The-Public-Radio/Embedded_Hardware/EAGLE_CAD/TestFixtures /PRTF01.brd

## EAGLE design EAGLE_CAD/TestFixtures /PRTF01.brd (2015-02-14)

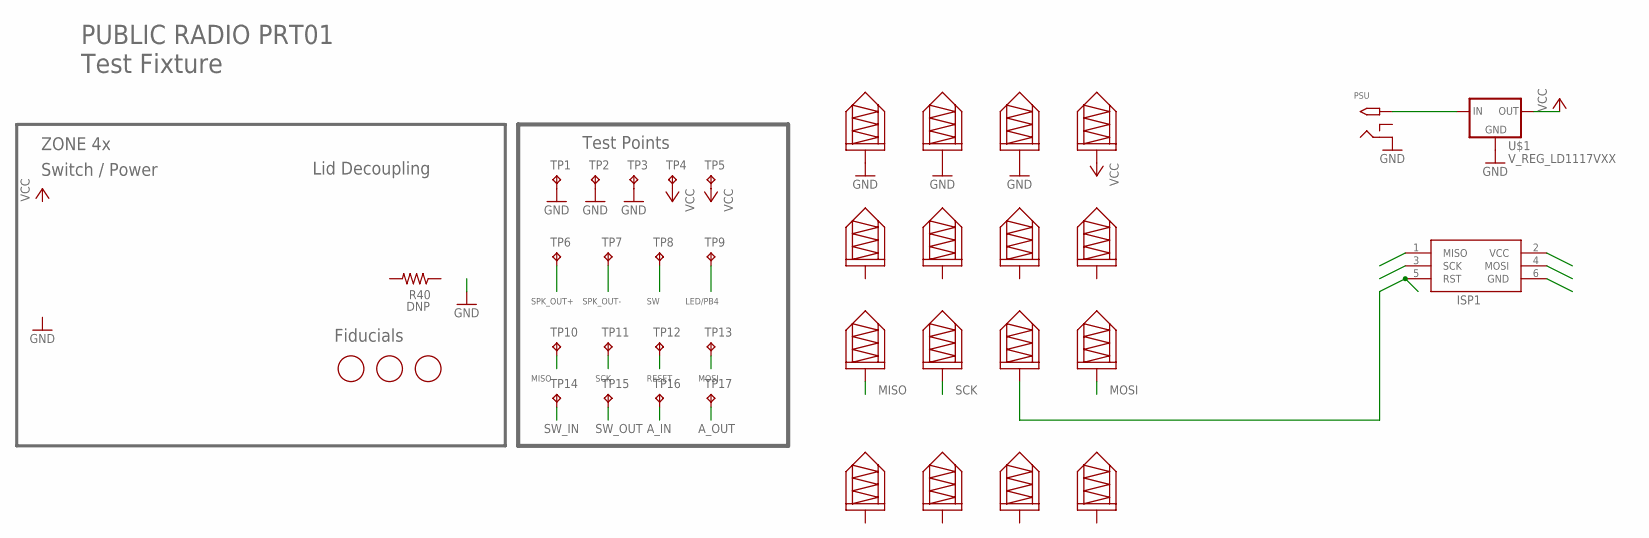
[picture p14: schematic PRTF01.sch]

Parts:
ISP1: AVRISP-6; AVRISP
MARK1, MARK2, MARK3: FIDUCIAL; FIDUCIAL_1MM
P1, P2, P3, P4, P6, P8, P9, P10, P11, P12, P13, P14, P15, P16, P17: 0908MILL_MAX_SPRINGPIN
PSU: 2.1MMJACKTHM; PJ-102A
R40: DNP; 0603_CPL; MFG_PN ERJ-3GEY0R00V
TP1, TP2, TP3, TP4, TP5, TP6, TP7, TP8, TP9, TP10, TP11, TP12, TP13, TP14, TP15, TP16, TP17: TPTP20R; TP20R
U$1: V_REG_LD1117VXX; 78XXL
U$P7: 0908MILL_MAX_SPRINGPIN

Connections:
!RST: TP10.TP
A_IN: TP16.TP
A_OUT: TP17.TP
GND: P1.P$1, P2.P$1, P3.P$1, PSU.RING, TP1.TP, TP2.TP, TP3.TP, U$1.IN (GND)
LED/PB4: TP9.TP
MISO: ISP1.1 (MISO), P10.P$1
MOSI: ISP1.4 (MOSI), P13.P$1
unnamed: PSU.TIP, U$1.OUT (IN)
RESET: ISP1.5 (RST), P12.P$1, TP12.TP
SCK: ISP1.3 (SCK), P11.P$1
SCLK: TP11.TP
SDIO: TP13.TP
SPK_OUT+: TP6.TP
SPK_OUT-: TP7.TP
SW: TP8.TP
SW_IN: TP14.TP
SW_OUT: TP15.TP
VCC: P4.P$1, TP4.TP, TP5.TP, U$1.GND (OUT)

Notes on the sheet:
Switch / Power
Lid Decoupling
PUBLIC RADIO PRT01 Test Fixture
Fiducials
Test Points
MISO
SCK
RESET
MOSI
ZONE 4x
