The-Public-Radio/Embedded_Hardware/EAGLE_CAD/TestFixtures /PRTF01.brd

## EAGLE design EAGLE_CAD/TestFixtures /PRTF01.brd (continued)

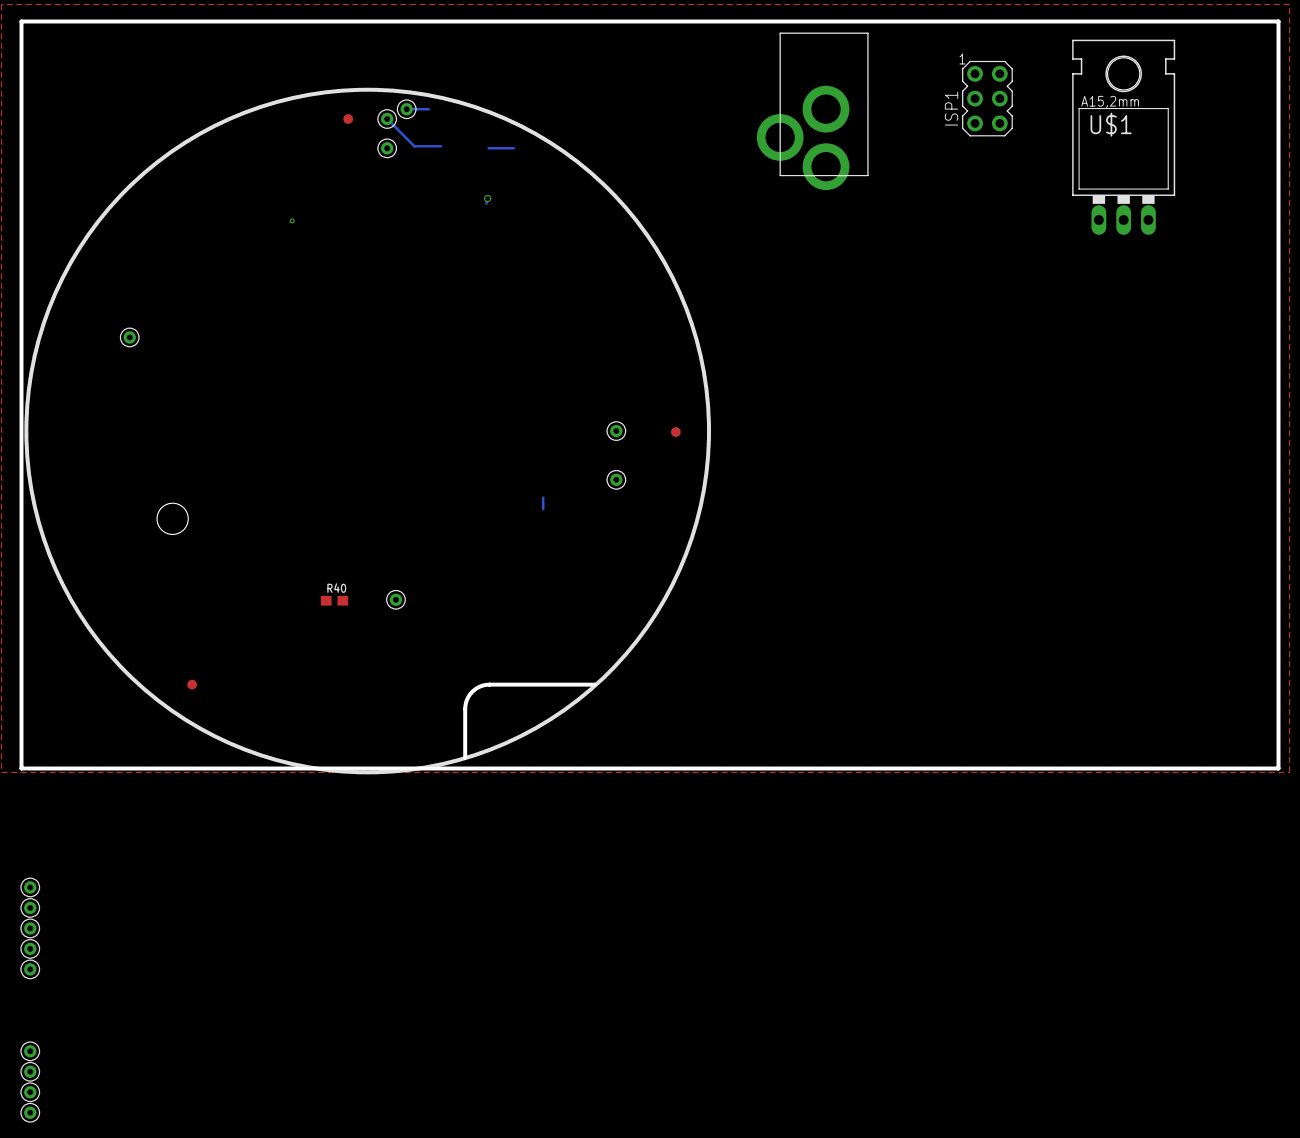
[picture p15: board PRTF01.brd from above]

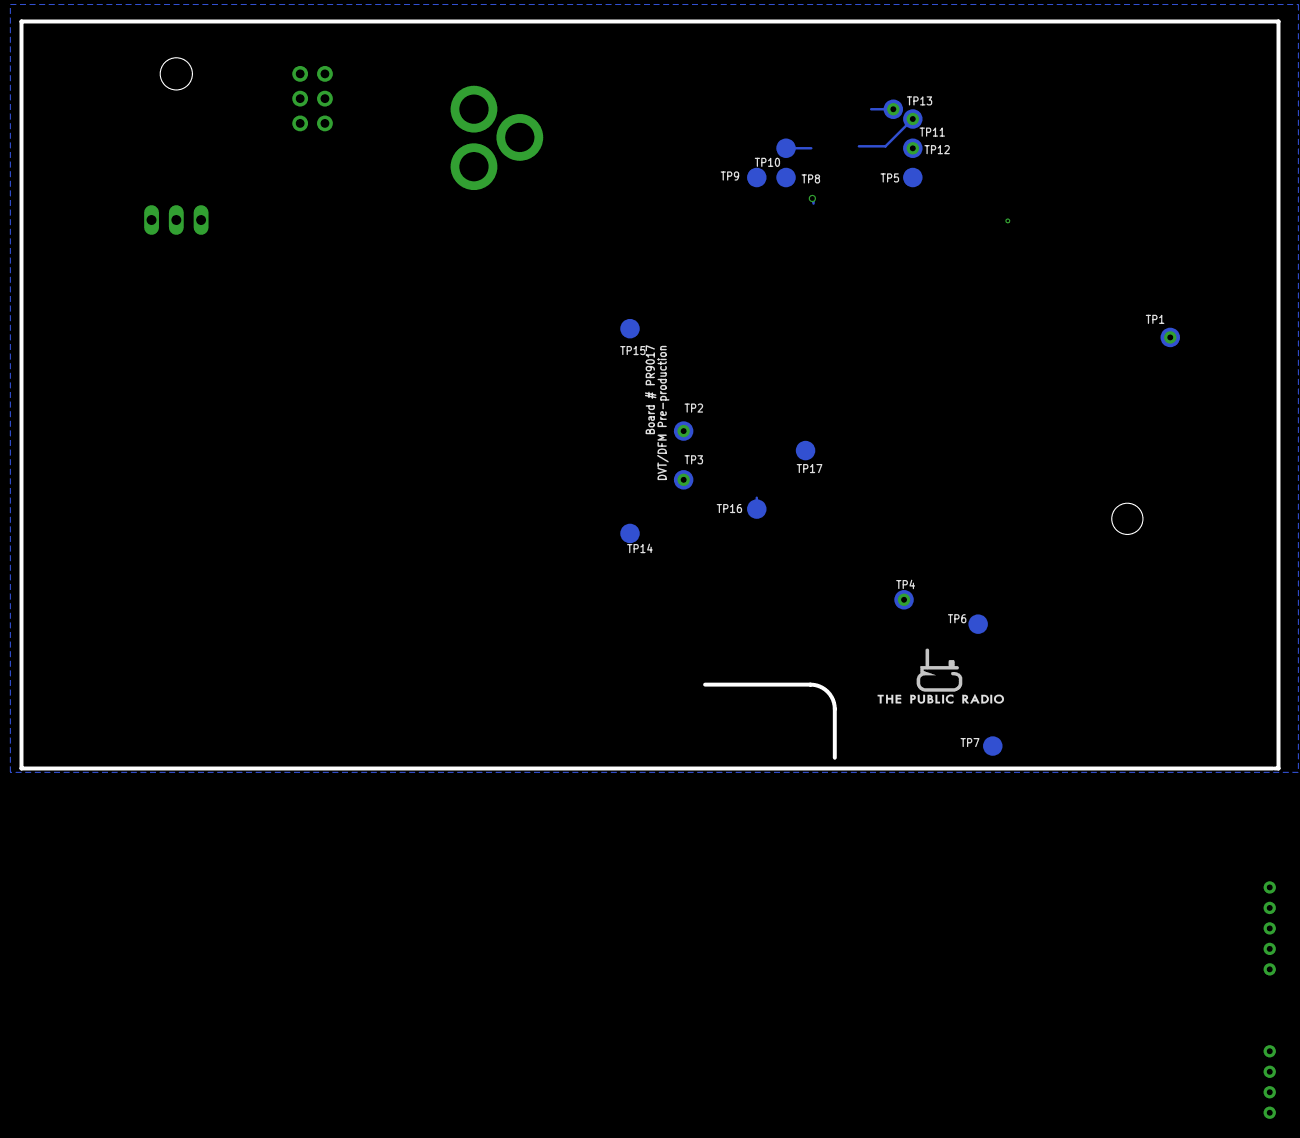
[picture p16: board PRTF01.brd from below]

Board: 2 copper layers, 128.9 x 76.6 mm, 40 parts (17 on the bottom side), 7 nets.
