The-Public-Radio/Embedded_Hardware/EAGLE_CAD/PR9018ProductionFiles/Eagle/PR9018.brd

## EAGLE design EAGLE_CAD/PR9018ProductionFiles/Eagle/PR9018.brd (2015-02-14)

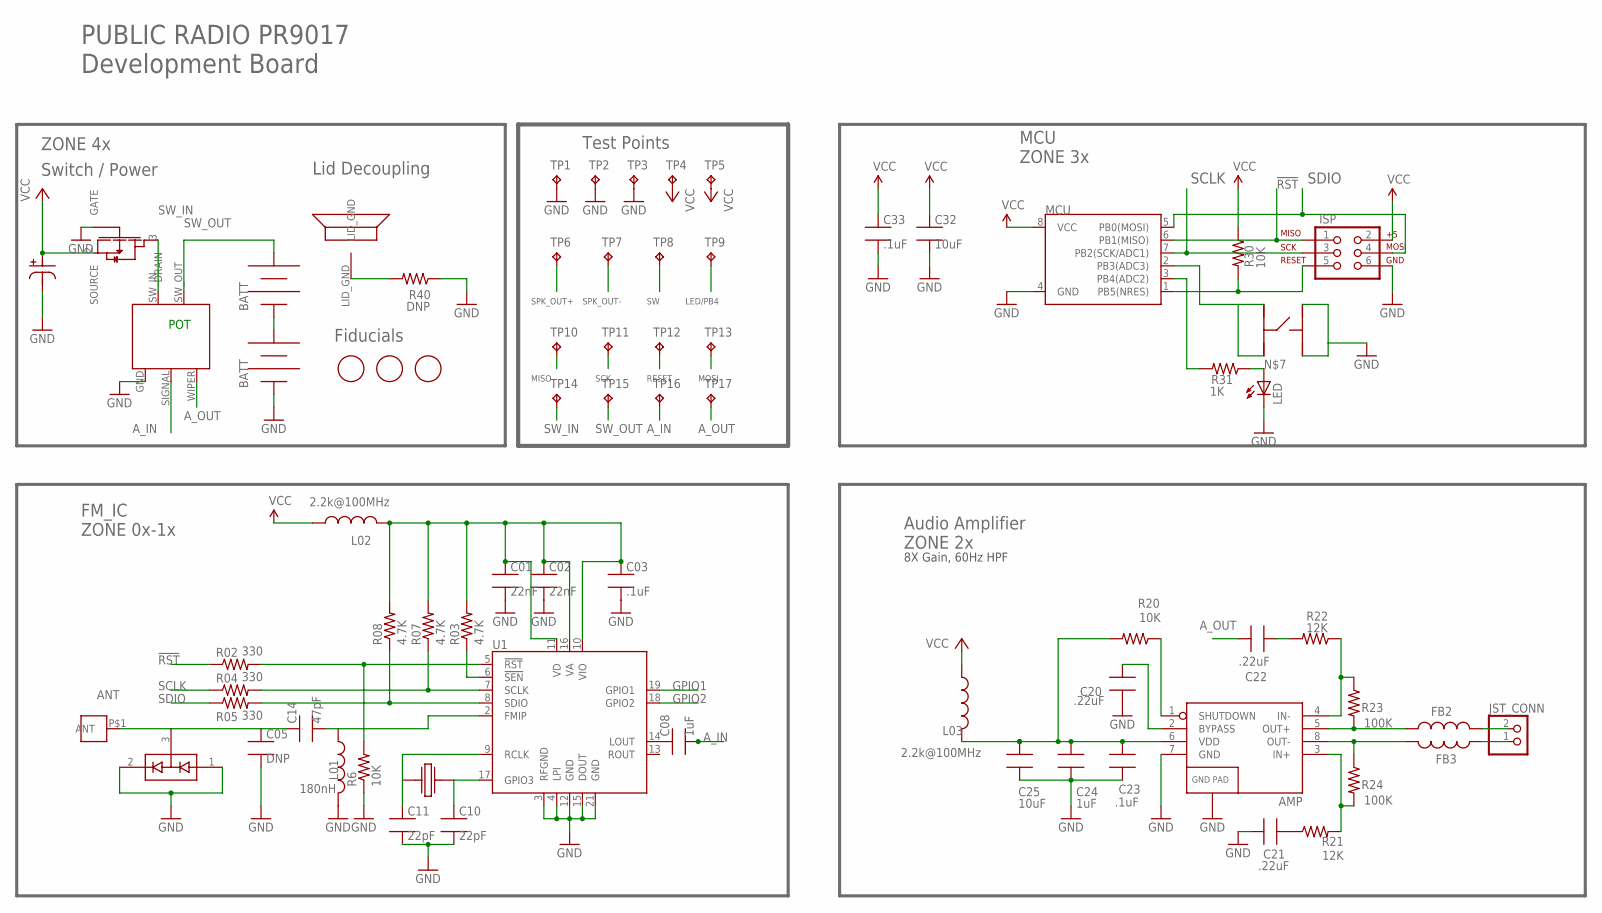
[picture p17: schematic PR9018.sch]

Parts:
AMP: TPA6203A1; 8-MSOP
ANT_MOUNT: DNP; M3_BOLT_HOLE
C01, C02: 22nF; 0603_CPL; VOLTAGE 16V; MFG_PN CL10B223KB8NNNC
C03, C23, C33: .1uF; 0603_CPL; VOLTAGE 16V; MFG_PN CL10B104KB8SFNC
C05: DNP; 0603_CPL; VOLTAGE 50V; MFG_PN DNP
C08, C24: 1uF; 0603_CPL; VOLTAGE 10V; MFG_PN CL10B105KP8NNNC
C10, C11: 22pF; 0603_CPL; VOLTAGE 50V; MFG_PN C1608C0G1H220J080AA
C14: 47pF; 0603_CPL; VOLTAGE 50V; MFG_PN CL10C470JB8NCNC
C20, C21, C22: .22uF; 0603_CPL; VOLTAGE 16V; MFG_PN C1608X7R1C224K080AC
C25, C32: 10uF; 0603_CPL; VOLTAGE 6.3V; MFG_PN CL10A106MQ8NNNC
C40: 220uF; NICHICON_UD_63; VOLTAGE 16V
D1: BAV99; SOT23_CPL; MFG_PN BAV99,215
FB2, FB3: L_SMT_0805_ADAFRUIT; 0805_ADAFRUIT; MFG_PN HI0805R800R-10
FET1: AO3435; SOT23_CPL; MFG_PN AO3435
ISP: AVR_SPI_PRG_6NS; 2X3-NS
JP5, JP6: BK-92_MPD_AA_BATT_CLIP; BK92_AA_BATT
JST_CONN: JST_2PIN-SMT-RA; JST-PH-2-SMT-RA
L01: 180nH; 0805_ADAFRUIT; MFG_PN AISC-0805-R18J-T
L02, L03: 2.2k@100MHz; 0603_CPL; MFG_PN HZ0603A222R-10
LED: LED; 0603_CPL; MFG_PN LY R976-PS-36
MARK1, MARK2, MARK3: FIDUCIAL; FIDUCIAL_1MM
MCU: ATTINY45TINY45-20-SMT; 8-SOIC
R1: RV170SF_TAIWANA_POT_SW; RV170SF_SW_POT
R02, R04, R05: 330; 0603_CPL; MFG_PN MCR03ERTJ331
R03, R07, R08: 4.7K; 0603_CPL; MFG_PN ERJ-3EKF4701V
R6, R20, R30: 10K; 0603_CPL; MFG_PN ERJ-3GEYJ103V
R21, R22: 12K; 0603_CPL; MFG_PN RMCF0603FT12K0
R23, R24: 100K; 0603_CPL; MFG_PN RMCF0603FT100K
R31: 1K; 0603_CPL; MFG_PN ERJ-3EKF1001V
R40: DNP; 0603_CPL; MFG_PN ERJ-3GEY0R00V
SPKR_PLACE: DNP; PR2023_SPKR_PLACE
SW1: C&K_PTS645; C&K_PTS645_SMT
TP1, TP2, TP3, TP4, TP5, TP6, TP7, TP8, TP9, TP10, TP11, TP12, TP13, TP14, TP15, TP16, TP17: TPTP20R; TP20R
U1: SI4702-C19-GMR; SI470X_20_QFN
X1: ABS25XTAL; 4-SOJ

Connections:
3.3V: C01.1, C02.1, C03.1, L02.2, R03.2, R07.2, R08.2, U1.10 (VIO), U1.11 (VD), U1.16 (VA)
!RST: ISP.1, MCU.6 (PB1(MISO)), R02.1, TP10.TP
!RST-L: R02.2, R6.2, U1.5 (!RST)
!SEN-L: R03.1, U1.6 (!SEN)
ANT: ANT_MOUNT.P$1, C05.1, C14.1, D1.3 (COM)
A_IN: C08.2, R1.SIGNAL, TP16.TP
A_OUT: C22.2, R1.WIPER, TP17.TP
GND: AMP.7 (GND), AMP.9 (GND), C01.2, C02.2, C03.2, C05.2, C10.2, C11.2, C20.1, C21.1, C23.2, C24.2, C25.2, C32.2, C33.2, C40.P$2, D1.1 (A1), D1.2 (C2), FET1.1 (GATE), ISP.6, JP6.NEG, JP6.NEG@2 (NEG), L01.2, LED.2 (C), MCU.4 (GND), R1.GND, R6.1, R40.1, SW1.P$1, SW1.P$2, TP1.TP, TP2.TP, TP3.TP, U1.3 (RFGND), U1.4 (LPI), U1.12 (GND), U1.15 (DOUT), U1.21 (GND)
GPIO1: U1.19 (GPIO1)
GPIO2: U1.18 (GPIO2)
LED/PB4: MCU.3 (PB4(ADC2)), R31.2, TP9.TP
unnamed: C11.1, U1.9 (RCLK), X1.P$1
unnamed: AMP.6 (VDD), C23.1, C24.1, C25.1, L03.2, R20.2
unnamed: C22.1, R22.2
unnamed: AMP.5 (OUT+), FB2.1, R23.2
unnamed: AMP.3 (IN+), R21.2, R24.2
unnamed: LED.1 (A), R31.1
unnamed: R40.2, SPKR_PLACE.LID_GND
unnamed: C08.1, U1.14 (LOUT)
unnamed: C10.1, U1.17 (GPIO3), X1.P$4
unnamed: AMP.8 (OUT-), FB3.2, R24.1
unnamed: AMP.2 (BYPASS), C20.2
unnamed: JP5.NEG, JP5.NEG@2 (NEG), JP6.POS, JP6.POS@2 (POS)
unnamed: AMP.4 (IN-), R22.1, R23.1
unnamed: C14.2, L01.1, U1.2 (FMIP)
unnamed: AMP.1 (SHUTDOWN), R20.1
unnamed: C21.2, R21.1
RESET: ISP.5, MCU.1 (PB5(NRES)), R30.2, TP12.TP
SCLK: ISP.3, MCU.7 (PB2(SCK/ADC1)), R04.1, TP11.TP
SCLK-L: R04.2, R07.1, U1.7 (SCLK)
SDIO: ISP.4, MCU.5 (PB0(MOSI)), R05.1, TP13.TP
SDIO-L: R05.2, R08.1, U1.8 (SDIO)
SPK_OUT+: FB2.2, JST_CONN.2 (1), TP6.TP
SPK_OUT-: FB3.1, JST_CONN.1 (2), TP7.TP
SW: MCU.2 (PB3(ADC3)), SW1.P$3, SW1.P$4, TP8.TP
SW_IN: FET1.3 (DRAIN), R1.SW_IN, TP14.TP
SW_OUT: JP5.POS, JP5.POS@2 (POS), R1.SW_OUT, TP15.TP
VCC: C32.1, C33.1, C40.P$1, FET1.2 (SOURCE), ISP.2, L02.1, L03.1, MCU.8 (VCC), R30.1, TP4.TP, TP5.TP

Notes on the sheet:
POT
FM_IC ZONE 0x-1x
Switch / Power
Lid Decoupling
Audio Amplifier ZONE 2x
MCU ZONE 3x
PUBLIC RADIO PR9017 Development Board
Fiducials
Test Points
MISO
SCK
RESET
MOSI
8X Gain, 60Hz HPF
ZONE 4x

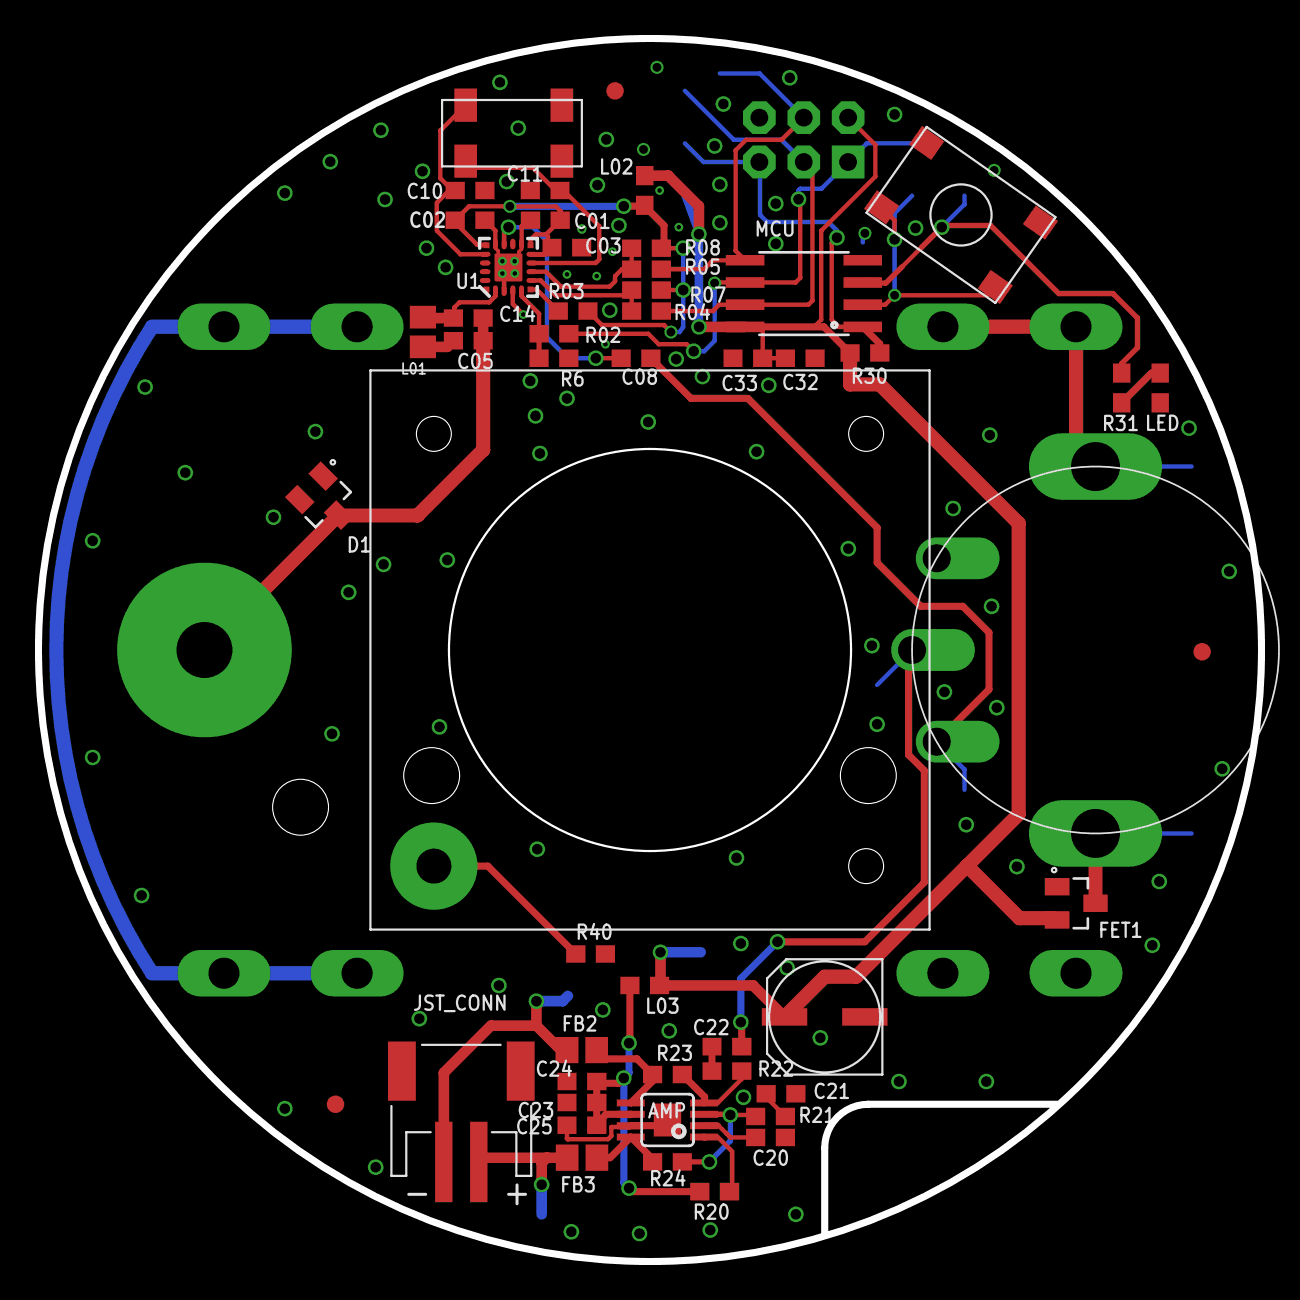
[picture p18: board PR9018.brd from above]

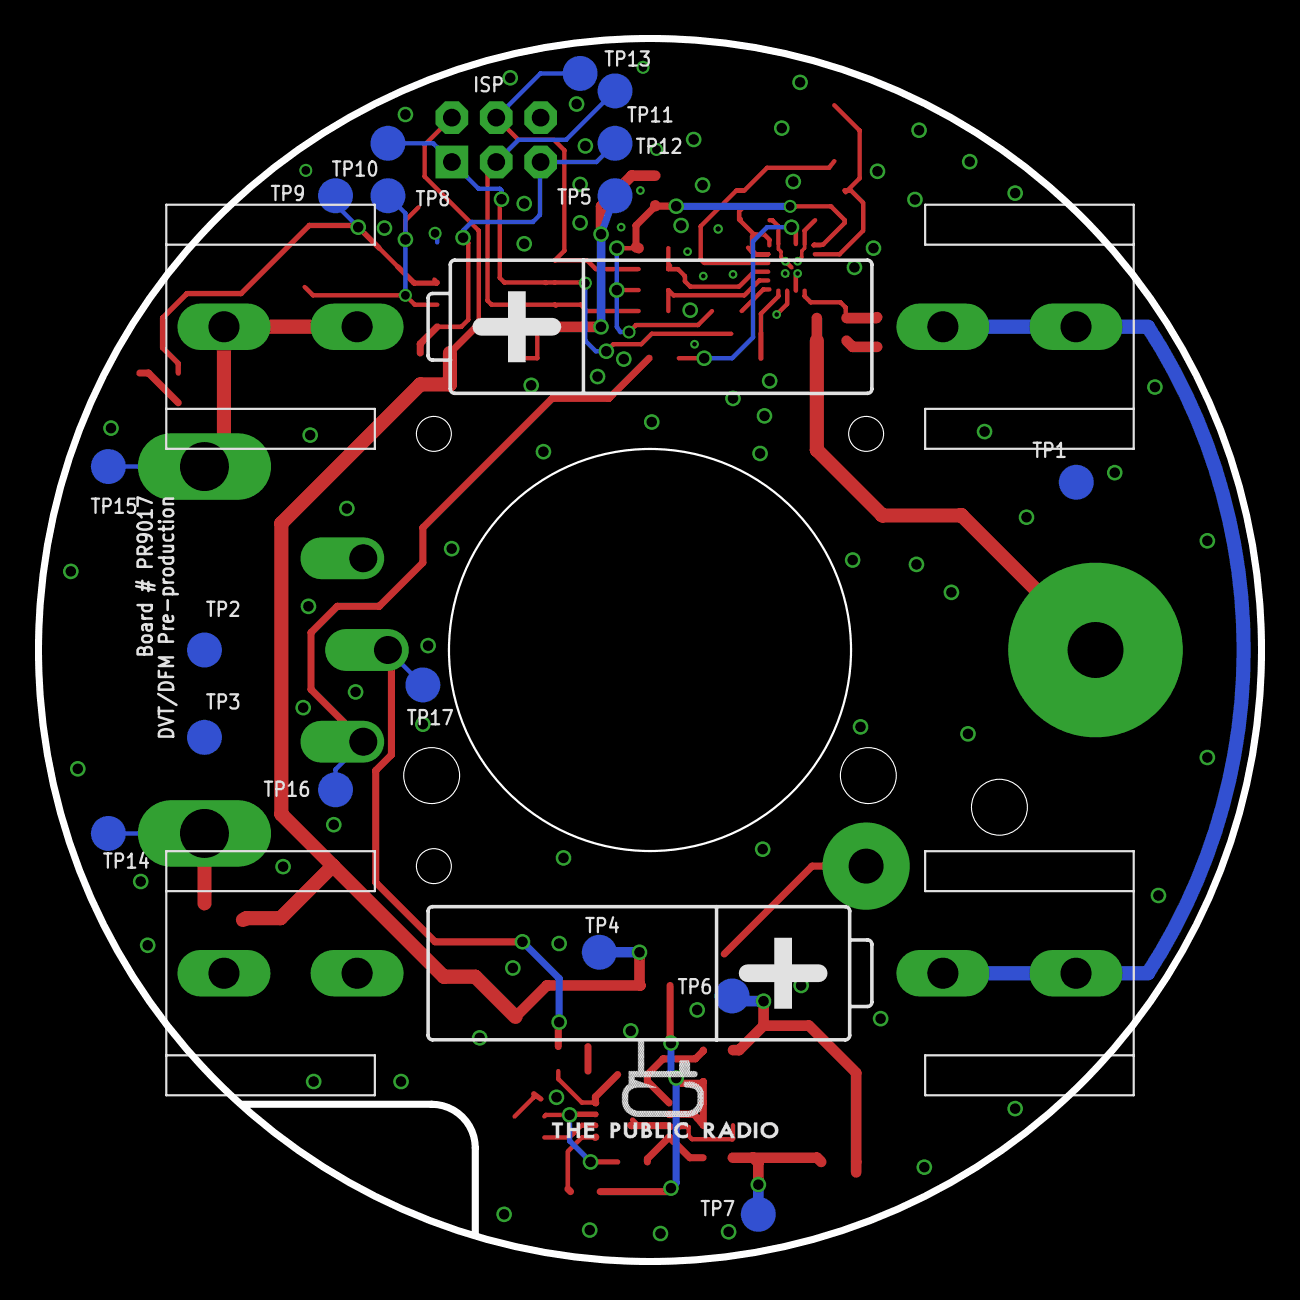
[picture p19: board PR9018.brd from below]

Board: 2 copper layers, 70.0 x 70.0 mm, 72 parts (20 on the bottom side), 36 nets.
