The-Public-Radio/Embedded_Hardware/EAGLE_CAD/PR9016.brd

## EAGLE design EAGLE_CAD/PR9016.brd (2015-01-31)

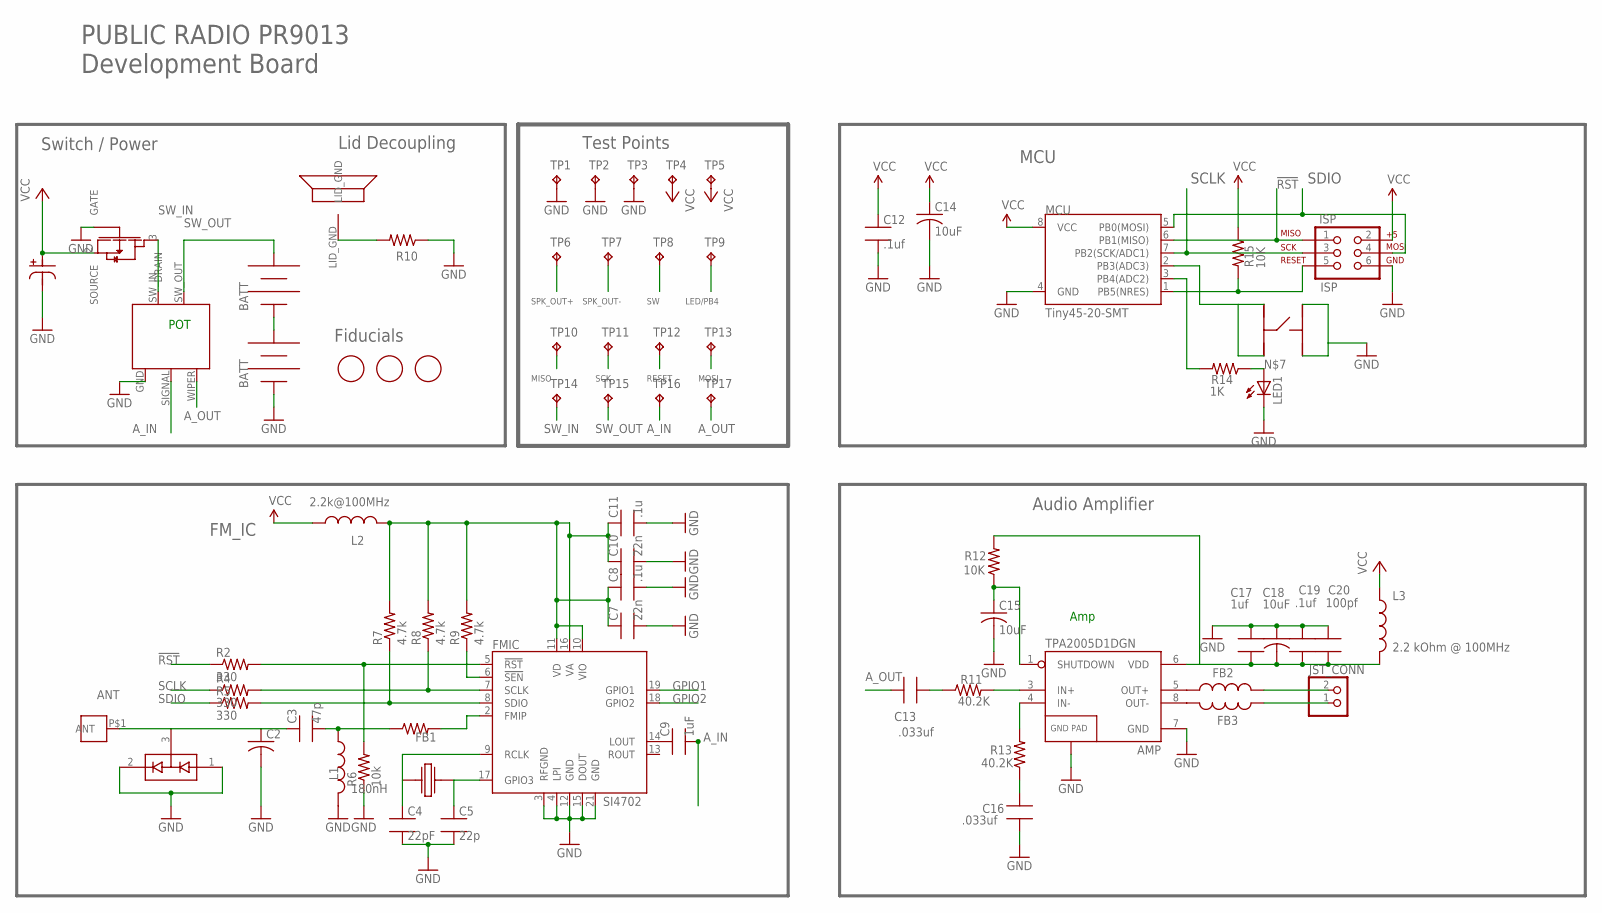
[picture p20: schematic PR9016.sch]

Parts:
AMP: TPA2005D1DGN; POWER-SOP8
ANT_MOUNT: M3_SCREW_POST
C1: 220uF; NICHICON_SERIESUD
C2: C-USC0805; C0805
C3: 47p; C0402_WORTHINGTON
C4: 22pF; C0402_WORTHINGTON
C5: 22p; C0402_WORTHINGTON
C7, C10: 22n; C0402_WORTHINGTON
C8, C11: .1u; C0402_WORTHINGTON
C9: 1uF; C0402_WORTHINGTON
C12, C19: .1uf; C0402_WORTHINGTON
C13, C16: .033uf; C0402_WORTHINGTON
C14, C15, C18: 10uF; C0603
C17: 1uf; C0402_WORTHINGTON
C20: 100pf; C0402_WORTHINGTON
D1: BAV99; SOT23
FB1: R-US_R0402; R0402
FB2, FB3: INDUCTOR0805; 0805
FET1: AO3435
FMIC: SI4702; SI470X
ISP: ISP; 2X3-NS
JP5, JP6: BK-92_MPD_AA_BATT_CLIP
JST_CONN: JST_2PIN-SMT-RA; JST-PH-2-SMT-RA
L1: 180nH; 0805
L2: 2.2k@100MHz; C0402_WORTHINGTON
L3: 2.2 kOhm @ 100MHz; C0402_WORTHINGTON
LED1: LEDSML0603; SML0603
MARK1, MARK2, MARK3: FIDUCIAL; FIDUCIAL_1MM
MCU: Tiny45-20-SMT; SO08-EIAJ
R1: RV170SF_TAIWANA_POT_SW
R2, R4, R5: 330; C0402_WORTHINGTON
R6: 10k; R0402
R7, R8, R9: 4.7k; C0402_WORTHINGTON
R10: R-US_R0805; R0805
R11, R13: 40.2K; C0402_WORTHINGTON
R12, R15: 10K; C0402_WORTHINGTON
R14: 1K; C0402_WORTHINGTON
SPKR_PLACE: CE32A_FOR_JST
SW1: C&K_PTS645; C&K_TACTILE_SWITCH
TP1, TP2, TP3, TP4, TP5, TP6, TP7, TP8, TP9, TP10, TP11, TP12, TP13, TP14, TP15, TP16, TP17: TPTP20R; TP20R
Y1: ABS25XTAL

Connections:
3.3V: C7.1, C8.1, C10.1, C11.1, FMIC.10 (VIO), FMIC.11 (VD), FMIC.16 (VA), L2.2, R7.2, R8.2, R9.2
!RST: ISP.1, MCU.6 (PB1(MISO)), R2.1, TP10.TP
!RST-L: FMIC.5 (!RST), R2.2, R6.2
!SEN-L: FMIC.6 (!SEN), R9.1
ANT: ANT_MOUNT.P$1, C2.1, C3.1, D1.3 (COM)
A_IN: C9.2, R1.SIGNAL, TP16.TP
A_OUT: C13.1, R1.WIPER, TP17.TP
GND: AMP.7 (GND), AMP.9 (GND), C1.P$2, C2.2, C4.2, C5.2, C7.2, C8.2, C10.2, C11.2, C12.2, C14.2, C15.2, C16.1, C17.1, C18.1, C19.1, C20.1, D1.1 (A1), D1.2 (C2), FET1.1 (GATE), FMIC.3 (RFGND), FMIC.4 (LPI), FMIC.12 (GND), FMIC.15 (DOUT), FMIC.21 (GND), ISP.6, JP6.NEG, JP6.NEG@2 (NEG), L1.2, LED1.C, MCU.4 (GND), R1.GND, R6.1, R10.1, SW1.P$1, SW1.P$2, TP1.TP, TP2.TP, TP3.TP
GPIO1: FMIC.19 (GPIO1)
GPIO2: FMIC.18 (GPIO2)
LED/PB4: MCU.3 (PB4(ADC2)), R14.2, TP9.TP
unnamed: C4.1, FMIC.9 (RCLK), Y1.P$1
unnamed: C13.2, R11.1
unnamed: AMP.3 (IN+), R11.2
unnamed: AMP.4 (IN-), R13.2
unnamed: FB1.2, FMIC.2 (FMIP)
unnamed: LED1.A, R14.1
unnamed: R10.2, SPKR_PLACE.LID_GND
unnamed: C9.1, FMIC.14 (LOUT)
unnamed: C5.1, FMIC.17 (GPIO3), Y1.P$4
unnamed: JP5.NEG, JP5.NEG@2 (NEG), JP6.POS, JP6.POS@2 (POS)
unnamed: C3.2, FB1.1, L1.1
unnamed: AMP.8 (OUT-), FB3.2
unnamed: AMP.6 (VDD), C17.2, C18.2, C19.2, C20.2, L3.2, R12.2
unnamed: AMP.5 (OUT+), FB2.1
unnamed: AMP.1 (SHUTDOWN), C15.1, R12.1
unnamed: C16.2, R13.1
RESET: ISP.5, MCU.1 (PB5(NRES)), R15.2, TP12.TP
SCLK: ISP.3, MCU.7 (PB2(SCK/ADC1)), R4.1, TP11.TP
SCLK-L: FMIC.7 (SCLK), R4.2, R8.1
SDIO: ISP.4, MCU.5 (PB0(MOSI)), R5.1, TP13.TP
SDIO-L: FMIC.8 (SDIO), R5.2, R7.1
SPK_OUT+: FB2.2, JST_CONN.2 (1), TP6.TP
SPK_OUT-: FB3.1, JST_CONN.1 (2), TP7.TP
SW: MCU.2 (PB3(ADC3)), SW1.P$3, SW1.P$4, TP8.TP
SW_IN: FET1.3 (DRAIN), R1.SW_IN, TP14.TP
SW_OUT: JP5.POS, JP5.POS@2 (POS), R1.SW_OUT, TP15.TP
VCC: C1.P$1, C12.1, C14.1, FET1.2 (SOURCE), ISP.2, L2.1, L3.1, MCU.8 (VCC), R15.1, TP4.TP, TP5.TP

Notes on the sheet:
Amp
POT
FM_IC
Switch / Power
Lid Decoupling
Audio Amplifier
MCU
PUBLIC RADIO PR9013 Development Board
Fiducials
Test Points
MISO
SCK
RESET
MOSI

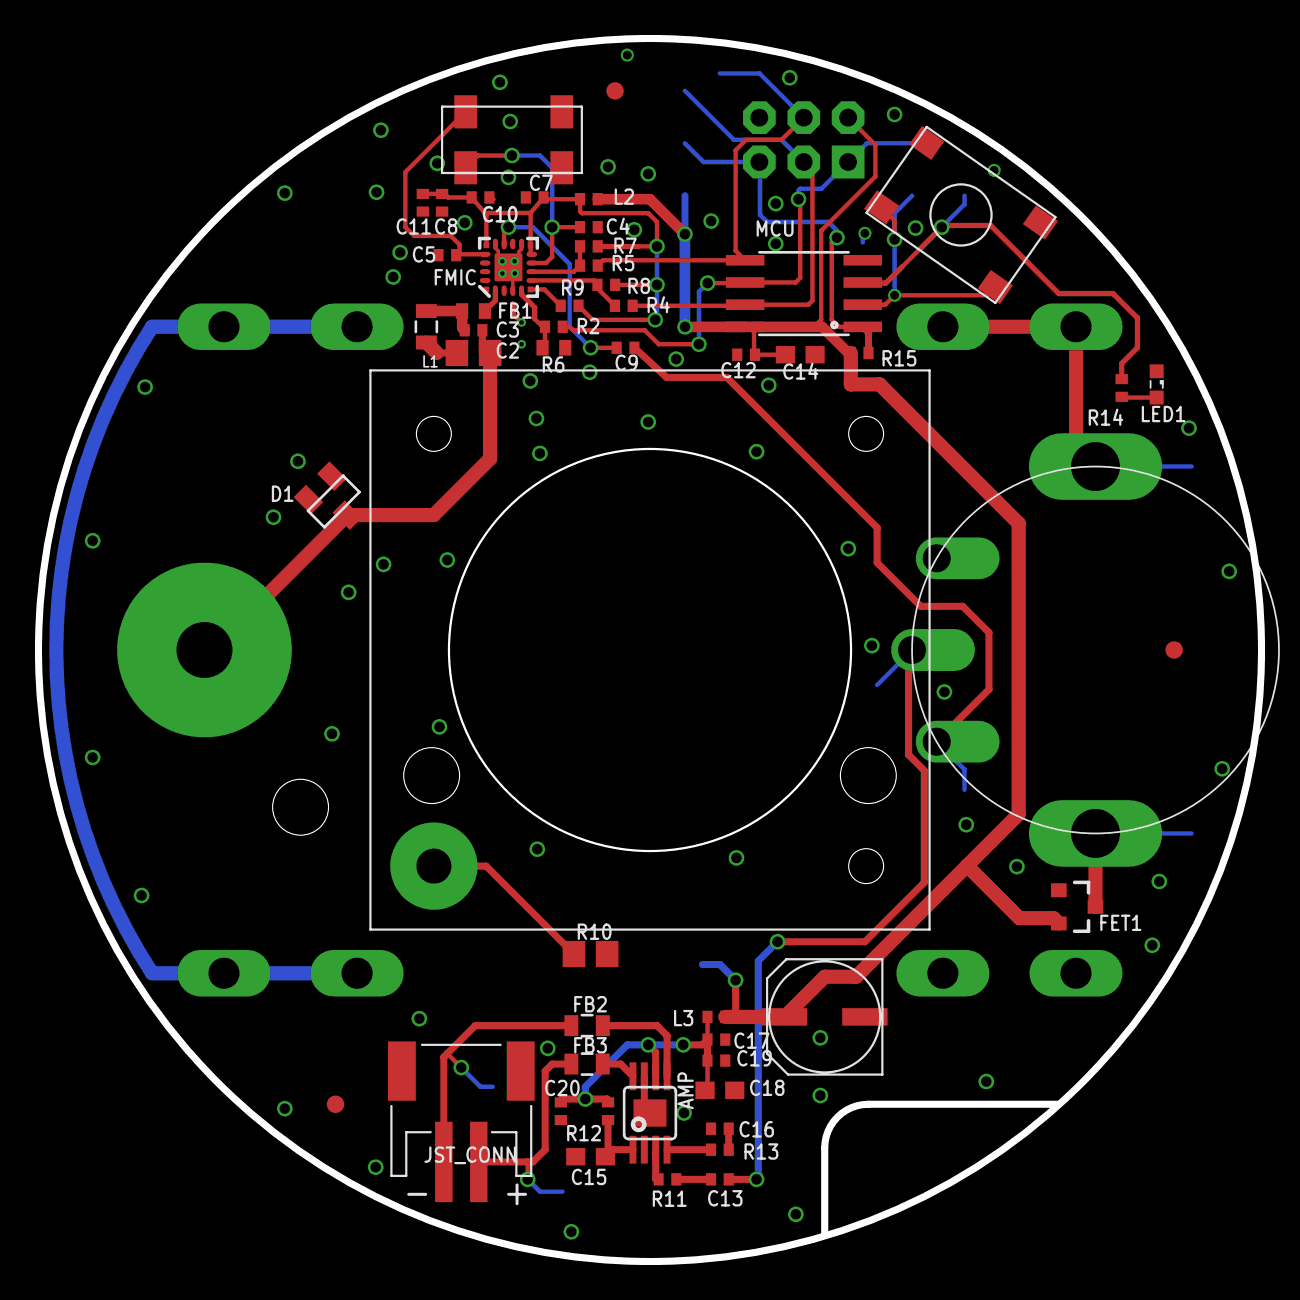
[picture p21: board PR9016.brd from above]

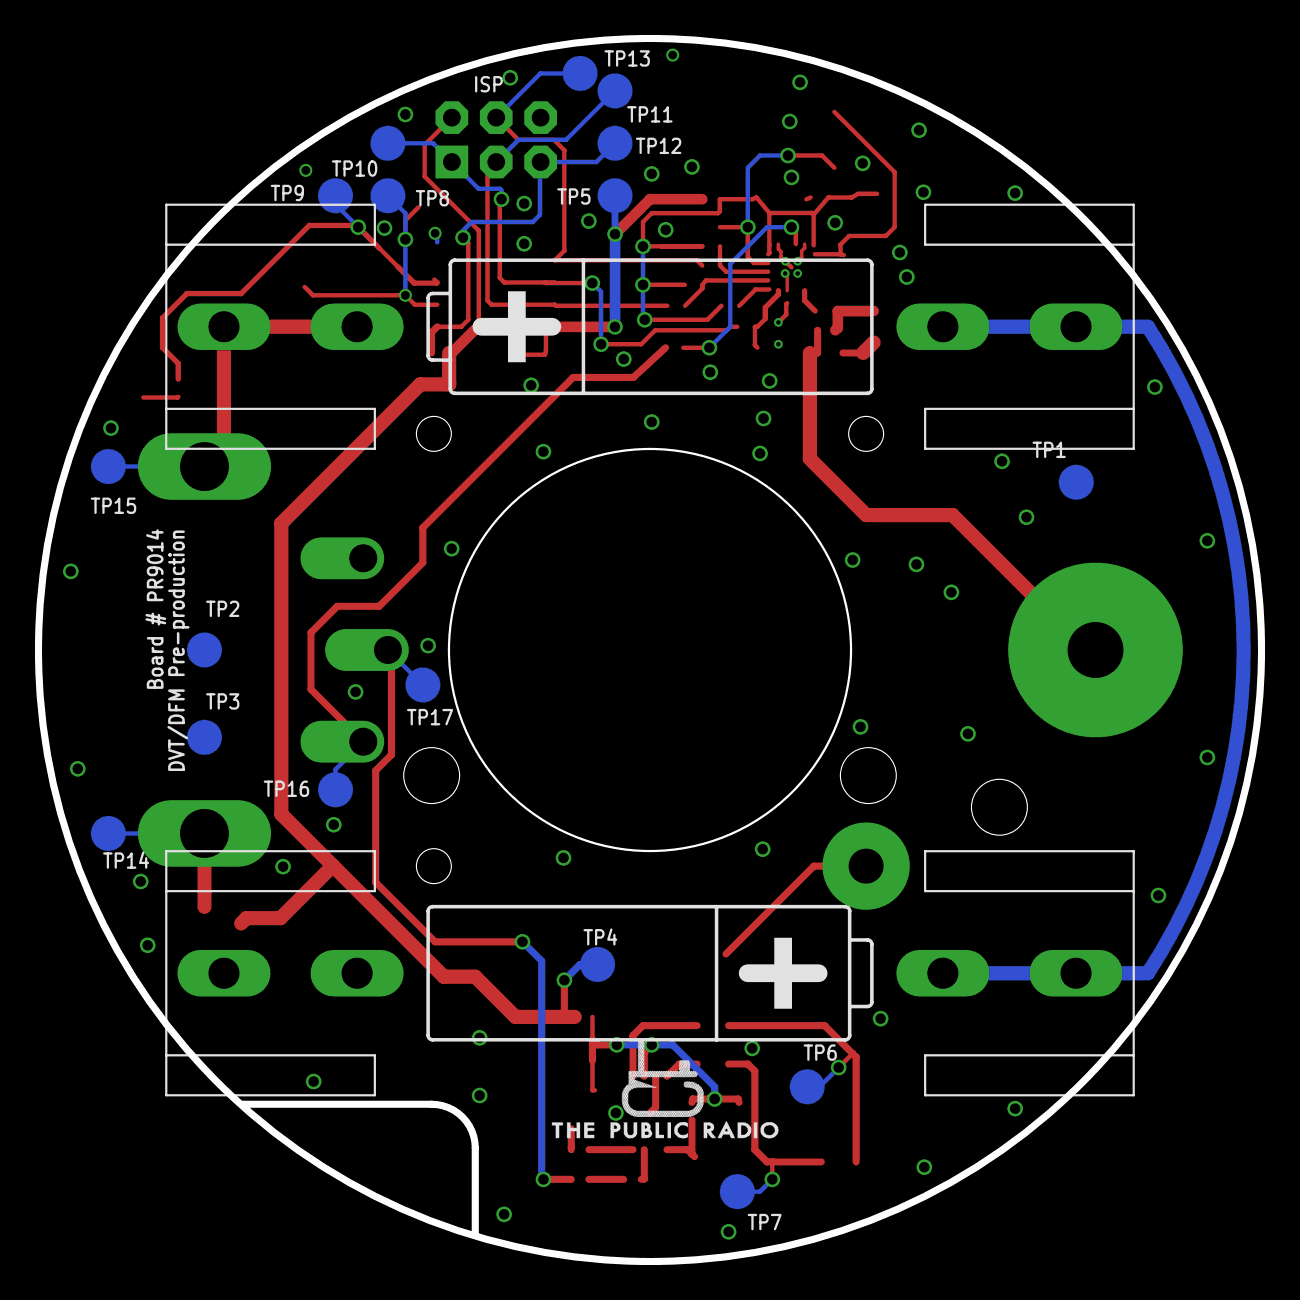
[picture p22: board PR9016.brd from below]

Board: 2 copper layers, 70.0 x 70.0 mm, 73 parts (20 on the bottom side), 36 nets.
