The-Public-Radio/Embedded_Hardware/PR9012Production_Files/EagleCAD/PR9012.brd

## EAGLE design PR9012Production_Files/EagleCAD/PR9012.brd (2014-12-22)

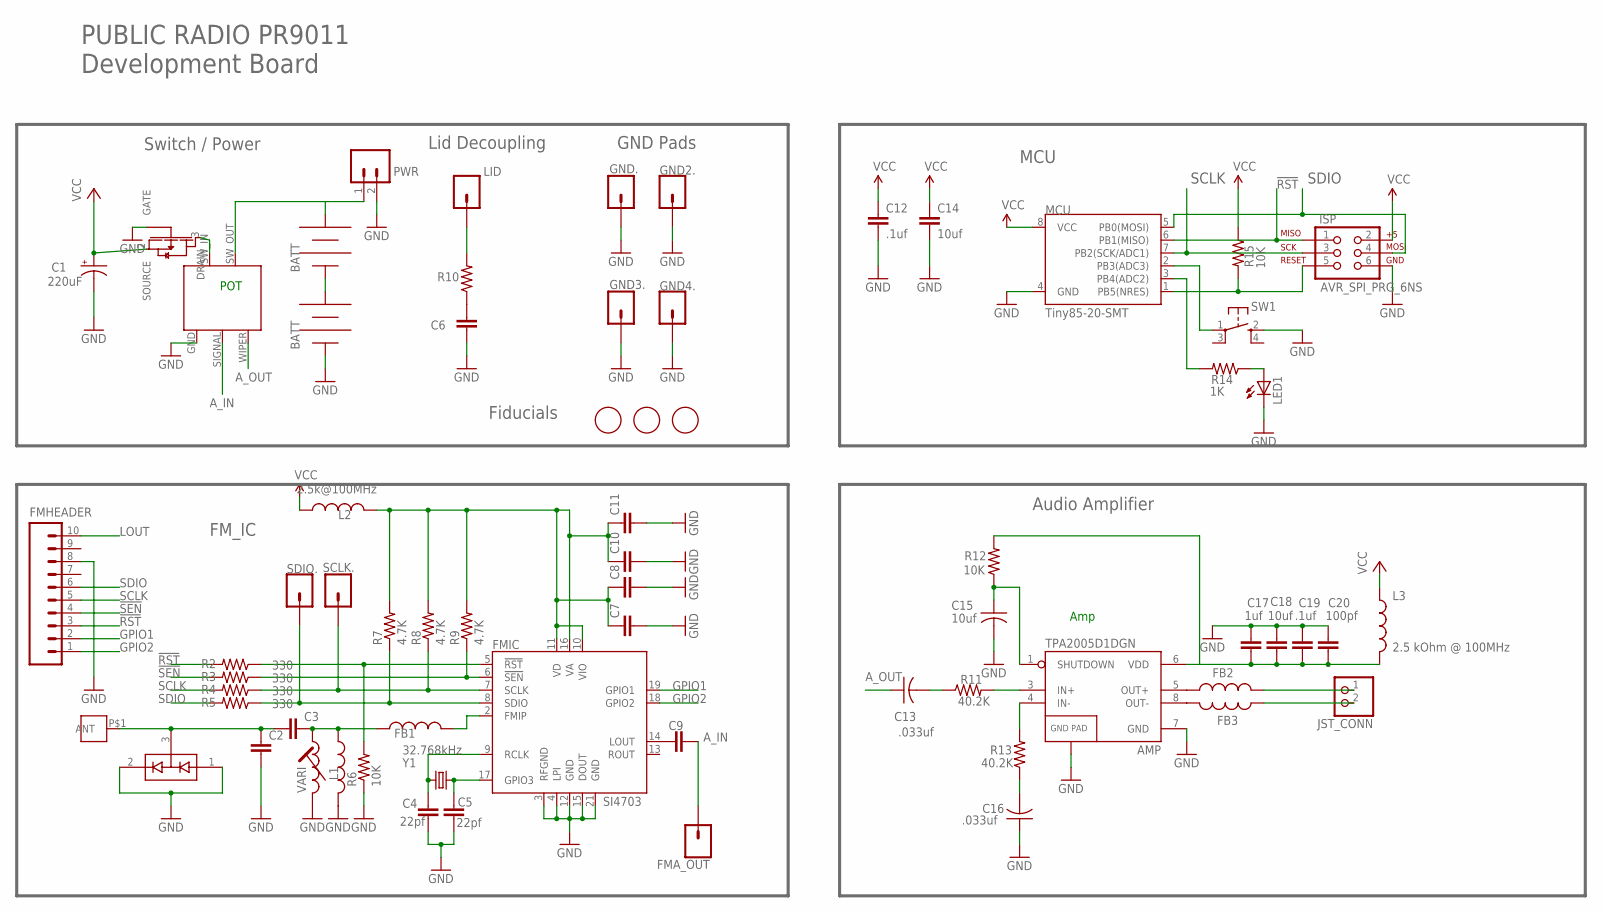
[picture p23: schematic PR9012.sch]

Parts:
AMP: TPA2005D1DGN; POWER-SOP8
C1: 220uF; PANASONIC_C
C2, C3, C7, C9: 1.0uF; 0805
C4, C5: 22pf; 0805
C6: CAP0805; 0805
C8: .1uF; 0805
C10: 22nF; 0805
C11: 4.7uF; 0805
C12, C19: .1uf; 0805
C13, C16: .033uf; C0603
C14, C18: 10uf; 0805
C15: 10uf; C0603
C17: 1uf; 0805
C20: 100pf; 0805
D1: BAV99; SOT23-3
FB1, FB2, FB3: INDUCTOR0805; 0805
FET1: SI2333DDS
FMA_OUT: M01PTH; 1X01
FMHEADER: M10LOCK; 1X10_LOCK
FMIC: SI4703; SPARKFUN_SI470X
GND2., GND3., GND4., GND.: M01PTH; 1X01
ISP: AVR_SPI_PRG_6NS; 2X3-NS
J1: M3_SCREW_POST
JP5, JP6: BK-92_MPD_AA_BATT_CLIP
JST_CONN: JST_2PIN-SMT-RA; JST-PH-2-SMT-RA
L1: INDUCTOR0805; 0805
L2: 2.5k@100MHz; 0603
L3: 2.5 kOhm @ 100MHz; 0603
LED1: LEDSML0603; SML0603
LID: M01PTH; 1X01
MCU: Tiny85-20-SMT; SO08-EIAJ
PWR: M02PTH3; 1X02_LONGPADS
R1: RV170SF_TAIWANA_POT_SW
R2, R3, R4, R5: 330; 0805
R6: 10K; 0805
R7, R8, R9: 4.7K; 0805
R10: RESISTOR0805-RES; 0805
R11, R13: 40.2K; R0603
R12, R15: 10K; R0603
R14: 1K; R0603
SCLK.: M01PTH; 1X01
SDIO.: M01PTH; 1X01
SW1: SPST_TACT-KMR2; KMR2
U$1, U$2, U$4: FIDUCIAL; FIDUCIAL_1MM
VARI: L-TRIM; 146/150
Y1: 32.768kHz; CRYSTAL-32KHZ-SMD

Connections:
3.3V: C7.1, C8.1, C10.1, C11.1, FMIC.10 (VIO), FMIC.11 (VD), FMIC.16 (VA), L2.2, R7.2, R8.2, R9.2
!RST: FMHEADER.3, ISP.1, MCU.6 (PB1(MISO)), R2.2
!RST-L: FMIC.5 (!RST), R2.1, R6.2
!SEN: FMHEADER.4, R3.2
!SEN-L: FMIC.6 (!SEN), R3.1, R9.1
A_IN: C9.2, FMA_OUT.1, R1.SIGNAL
A_OUT: C13.1, R1.WIPER
GND: AMP.7 (GND), AMP.9 (GND), C1.-, C2.2, C4.2, C5.2, C6.2, C7.2, C8.2, C10.2, C11.2, C12.2, C14.2, C15.2, C16.1, C17.1, C18.1, C19.1, C20.1, D1.1 (A1), D1.2 (C2), FET1.1 (GATE), FMHEADER.8, FMIC.3 (RFGND), FMIC.4 (LPI), FMIC.12 (GND), FMIC.15 (DOUT), FMIC.21 (GND), GND2..1, GND3..1, GND4..1, GND..1, ISP.6, JP6.NEG, JP6.NEG@2 (NEG), L1.2, LED1.C, MCU.4 (GND), PWR.2, R1.GND, R6.1, SW1.2 (S), VARI.P$1 (START)
GPIO1: FMHEADER.2, FMIC.19 (GPIO1)
GPIO2: FMHEADER.1, FMIC.18 (GPIO2)
LOUT: C9.1, FMHEADER.10, FMIC.14 (LOUT)
unnamed: C4.1, FMIC.9 (RCLK), Y1.X2 (2)
unnamed: C5.1, FMIC.17 (GPIO3), Y1.X1 (1)
unnamed: C13.2, R11.1
unnamed: AMP.3 (IN+), R11.2
unnamed: AMP.4 (IN-), R13.2
unnamed: FB1.2, FMIC.2 (FMIP)
unnamed: LED1.A, R14.1
unnamed: LID.1, R10.2
unnamed: FB2.2, JST_CONN.1 (2)
unnamed: MCU.2 (PB3(ADC3)), SW1.1
unnamed: MCU.3 (PB4(ADC2)), R14.2
unnamed: JP5.NEG, JP5.NEG@2 (NEG), JP6.POS, JP6.POS@2 (POS)
unnamed: C2.1, C3.1, D1.3 (COM), J1.P$1
unnamed: JP5.POS, JP5.POS@2 (POS), PWR.1, R1.SW_OUT
unnamed: C3.2, FB1.1, L1.1, VARI.P$2 (END)
unnamed: AMP.8 (OUT-), FB3.2
unnamed: AMP.6 (VDD), C17.2, C18.2, C19.2, C20.2, L3.2, R12.2
unnamed: AMP.5 (OUT+), FB2.1
unnamed: AMP.1 (SHUTDOWN), C15.1, R12.1
unnamed: C16.2, R13.1
unnamed: FET1.3 (DRAIN), R1.SW_IN
unnamed: C6.1, R10.1
OUT-: FB3.1, JST_CONN.2 (1)
PB5: ISP.5, MCU.1 (PB5(NRES)), R15.2
SCLK: FMHEADER.5, ISP.3, MCU.7 (PB2(SCK/ADC1)), R4.2
SCLK-L: FMIC.7 (SCLK), R4.1, R8.1, SCLK..1
SDIO: FMHEADER.6, ISP.4, MCU.5 (PB0(MOSI)), R5.2
SDIO-L: FMIC.8 (SDIO), R5.1, R7.1, SDIO..1
VCC: C1.+, C12.1, C14.1, FET1.2 (SOURCE), ISP.2, L2.1, L3.1, MCU.8 (VCC), R15.1

Notes on the sheet:
Amp
POT
FM_IC
Switch / Power
Lid Decoupling
Audio Amplifier
MCU
PUBLIC RADIO PR9011 Development Board
GND Pads
Fiducials

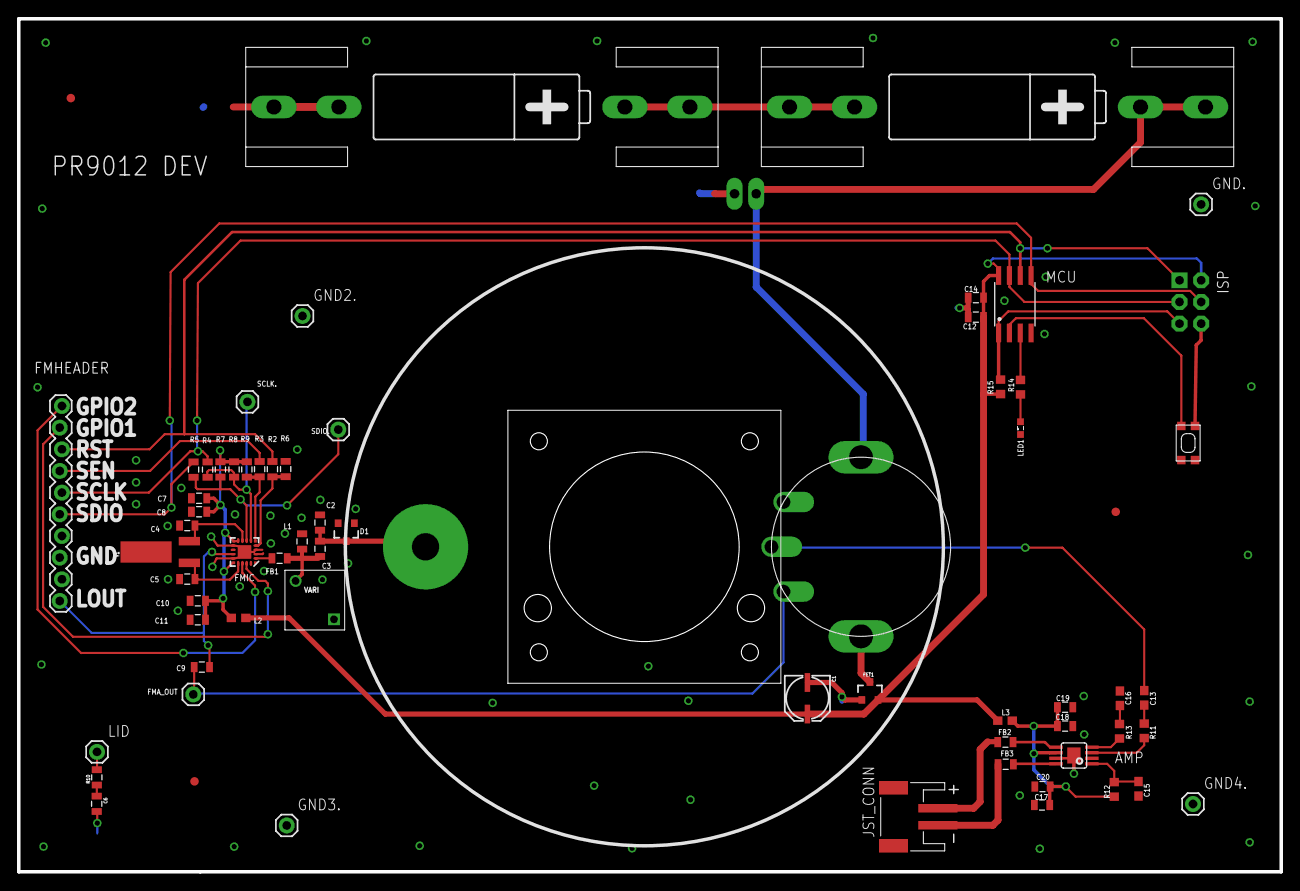
[picture p24: board PR9012.brd from above]

Board: 2 copper layers, 148.0 x 100.0 mm, 69 parts (0 on the bottom side), 40 nets.

Other parts of the board:
SPEAKER: CE32A_FOR_JST
