The-Public-Radio/Embedded_Hardware/EAGLE_CAD/PR9010.brd

## EAGLE design EAGLE_CAD/PR9010.brd (2014-12-06)

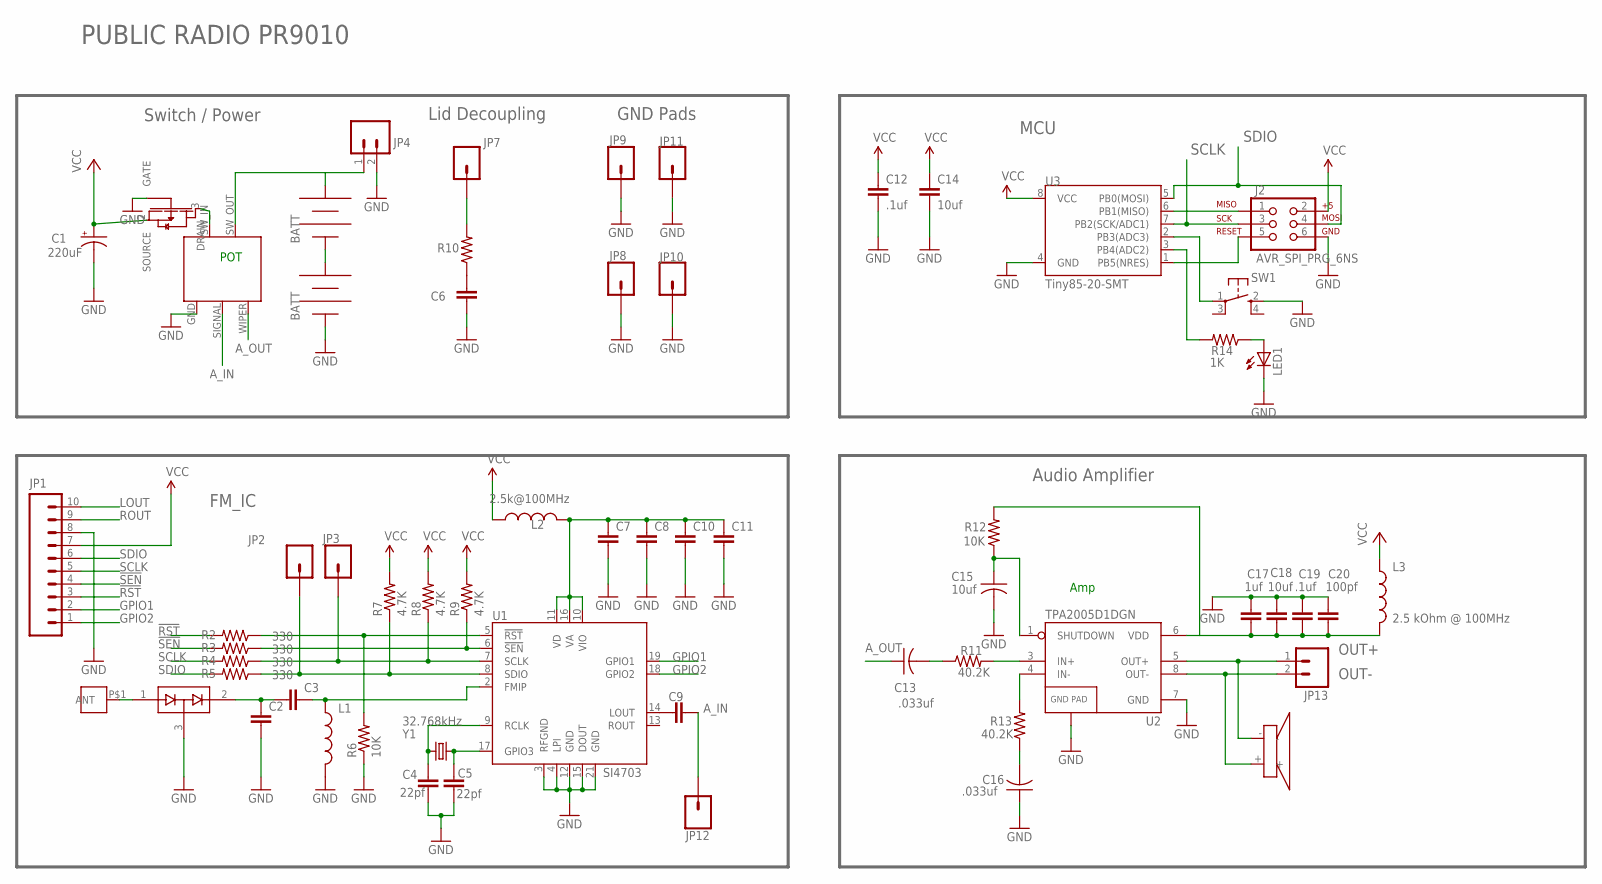
[picture p25: schematic PR9010.sch]

Parts:
C1: 220uF; PANASONIC_C
C2, C3, C7, C8, C9, C10, C11: 1.0uF; 0805
C4, C5: 22pf; 0805
C6: CAP0805; 0805
C12, C19: .1uf; 0805
C13, C16: .033uf; C0603
C14, C18: 10uf; 0805
C15: 10uf; C0603
C17: 1uf; 0805
C20: 100pf; 0805
D1: BAV99; SOT23
FET1: SI2333DDS
J1: M3_SCREW_POST
J2: AVR_SPI_PRG_6NS; 2X3-NS
JP1: M10"; 1X10
JP2, JP3, JP7, JP8, JP9, JP10, JP11, JP12: M01PTH; 1X01
JP4, JP13: M02PTH3; 1X02_LONGPADS
JP5, JP6: BK-92_MPD_AA_BATT_CLIP
L1: INDUCTOR0805; 0805
L2: 2.5k@100MHz; 0603
L3: 2.5 kOhm @ 100MHz; 0603
LED1: LEDSML0603; SML0603
R1: RV170SF_TAIWANA_POT_SW
R2, R3, R4, R5: 330; 0805
R6: 10K; 0805
R7, R8, R9: 4.7K; 0805
R10: RESISTOR0805-RES; 0805
R11, R13: 40.2K; R0603
R12: 10K; R0603
R14: 1K; R0603
SW1: SPST_TACT-KMR2; KMR2
U1: SI4703; SPARKFUN_SI470X
U2: TPA2005D1DGN; POWER-SOP8
U3: Tiny85-20-SMT; SO08-EIAJ
U$3: CE32A_DAYTON_SPKR
Y1: 32.768kHz; CRYSTAL-32KHZ-SMD

Connections:
3.3V: JP1.7, R7.2, R8.2, R9.2
!RST: JP1.3, R2.2
!RST-L: R2.1, R6.2, U1.5 (!RST)
!SEN: JP1.4, R3.2
!SEN-L: R3.1, R9.1, U1.6 (!SEN)
A_IN: C9.2, JP12.1, R1.SIGNAL
A_OUT: C13.1, R1.WIPER
GND: C1.-, C2.2, C4.2, C5.2, C6.2, C7.2, C8.2, C10.2, C11.2, C12.2, C14.2, C15.2, C16.1, C17.1, C18.1, C19.1, C20.1, D1.3 (COM), FET1.1 (GATE), J2.6, JP1.8, JP4.2, JP6.NEG, JP6.NEG@2 (NEG), JP8.1, JP9.1, JP10.1, JP11.1, L1.2, LED1.C, R1.GND, R6.1, SW1.2 (S), U1.3 (RFGND), U1.4 (LPI), U1.12 (GND), U1.15 (DOUT), U1.21 (GND), U2.7 (GND), U2.9 (GND), U3.4 (GND)
GPIO1: JP1.2, U1.19 (GPIO1)
GPIO2: JP1.1, U1.18 (GPIO2)
LOUT: C9.1, JP1.10, U1.14 (LOUT)
unnamed: C4.1, U1.9 (RCLK), Y1.X2 (2)
unnamed: C5.1, U1.17 (GPIO3), Y1.X1 (1)
unnamed: C13.2, R11.1
unnamed: R11.2, U2.3 (IN+)
unnamed: R13.2, U2.4 (IN-)
unnamed: C3.2, L1.1, U1.2 (FMIP)
unnamed: LED1.A, R14.1
unnamed: JP7.1, R10.2
unnamed: C7.1, C8.1, C10.1, C11.1, L2.2, U1.10 (VIO), U1.11 (VD), U1.16 (VA)
unnamed: SW1.1, U3.2 (PB3(ADC3))
unnamed: R14.2, U3.3 (PB4(ADC2))
unnamed: JP5.NEG, JP5.NEG@2 (NEG), JP6.POS, JP6.POS@2 (POS)
unnamed: D1.1 (A1), J1.P$1
unnamed: JP4.1, JP5.POS, JP5.POS@2 (POS), R1.SW_OUT
unnamed: C2.1, C3.1, D1.2 (C2)
unnamed: C17.2, C18.2, C19.2, C20.2, L3.2, R12.2, U2.6 (VDD)
unnamed: C15.1, R12.1, U2.1 (SHUTDOWN)
unnamed: C16.2, R13.1
unnamed: FET1.3 (DRAIN), R1.SW_IN
unnamed: C6.1, R10.1
OUT+: JP13.1, U2.5 (OUT+), U$3.-
OUT-: JP13.2, U2.8 (OUT-), U$3.+
PB1: J2.1, U3.6 (PB1(MISO))
PB5: J2.5, U3.1 (PB5(NRES))
ROUT: JP1.9
SCLK: J2.3, JP1.5, R4.2, U3.7 (PB2(SCK/ADC1))
SCLK-L: JP3.1, R4.1, R8.1, U1.7 (SCLK)
SDIO: J2.4, JP1.6, R5.2, U3.5 (PB0(MOSI))
SDIO-L: JP2.1, R5.1, R7.1, U1.8 (SDIO)
VCC: C1.+, C12.1, C14.1, FET1.2 (SOURCE), J2.2, L2.1, L3.1, U3.8 (VCC)

Notes on the sheet:
Amp
POT
FM_IC
Switch / Power
Lid Decoupling
Audio Amplifier
MCU
PUBLIC RADIO PR9010
GND Pads

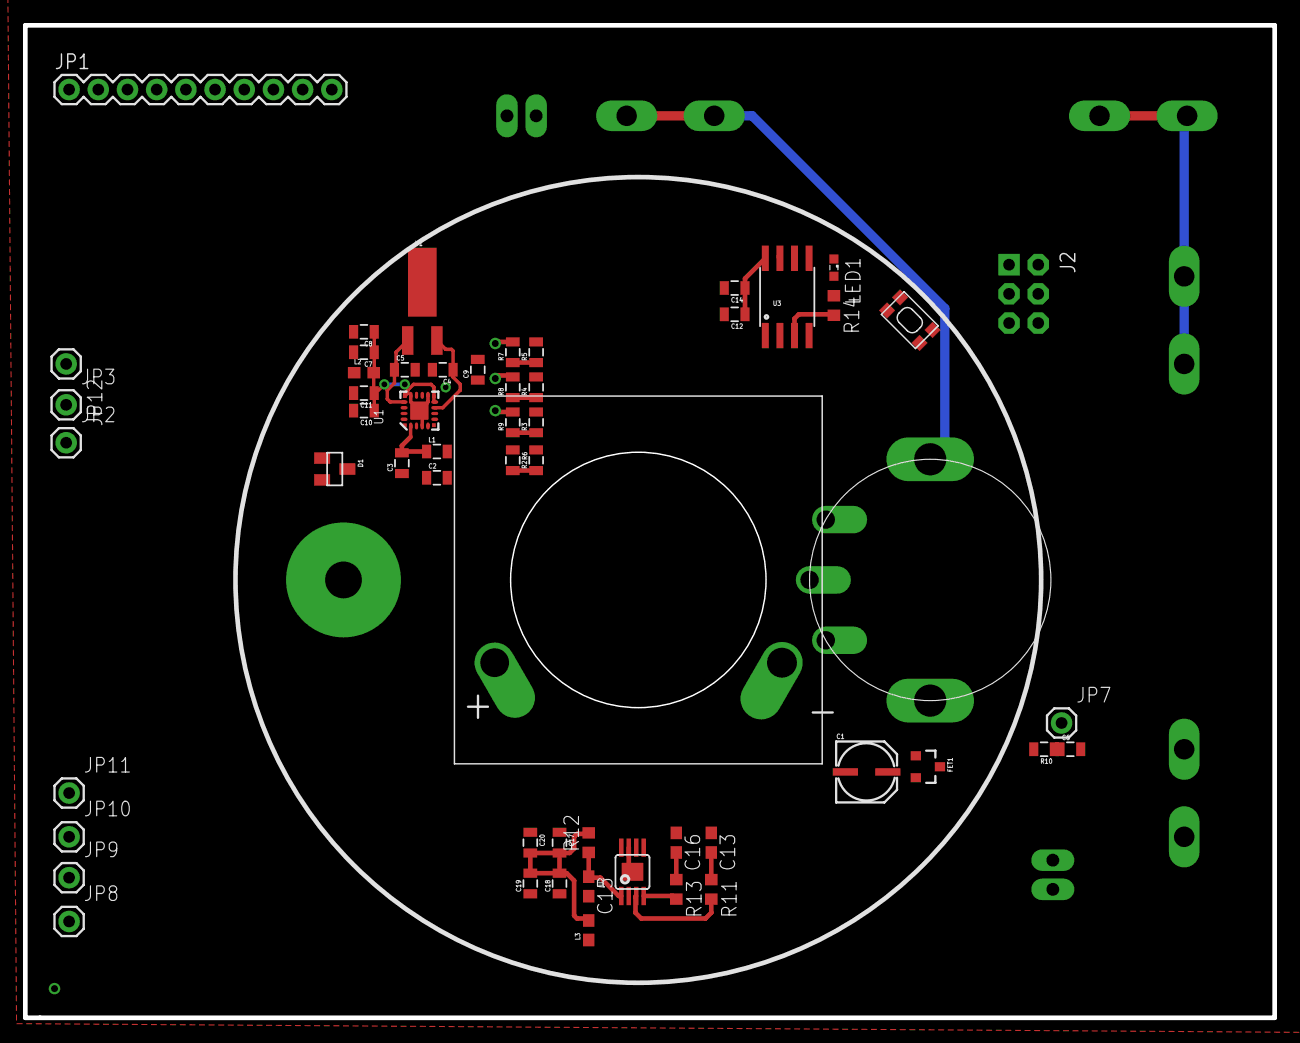
[picture p26: board PR9010.brd from above]

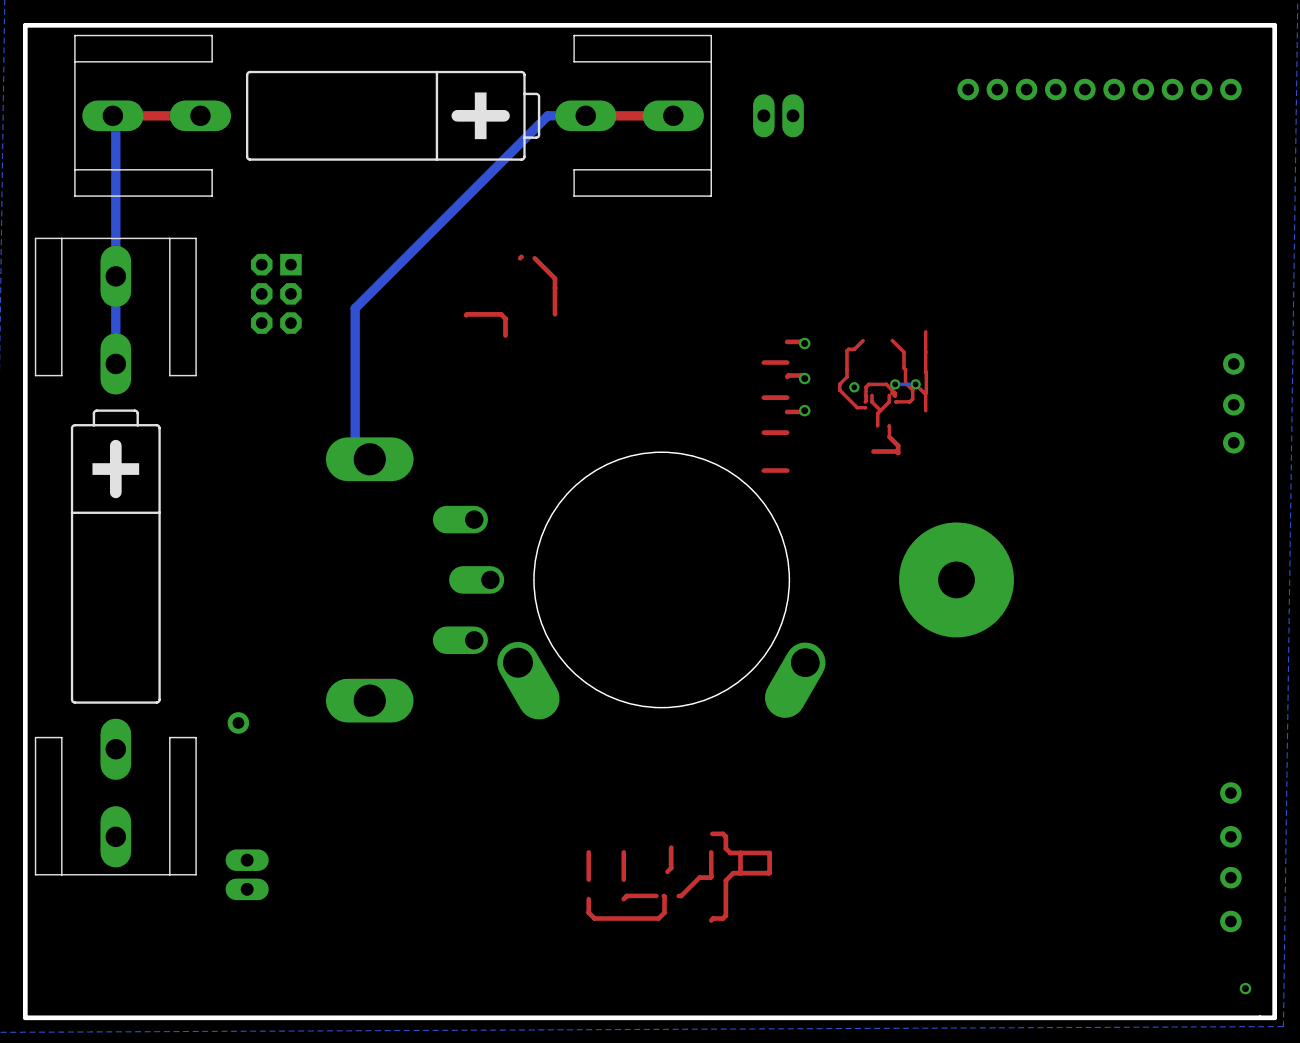
[picture p27: board PR9010.brd from below]

Board: 2 copper layers, 108.7 x 86.4 mm, 61 parts (2 on the bottom side), 40 nets.
