The-Public-Radio/Embedded_Hardware/EAGLE_CAD/PR5009.brd

## EAGLE design EAGLE_CAD/PR5009.brd (2014-09-24)

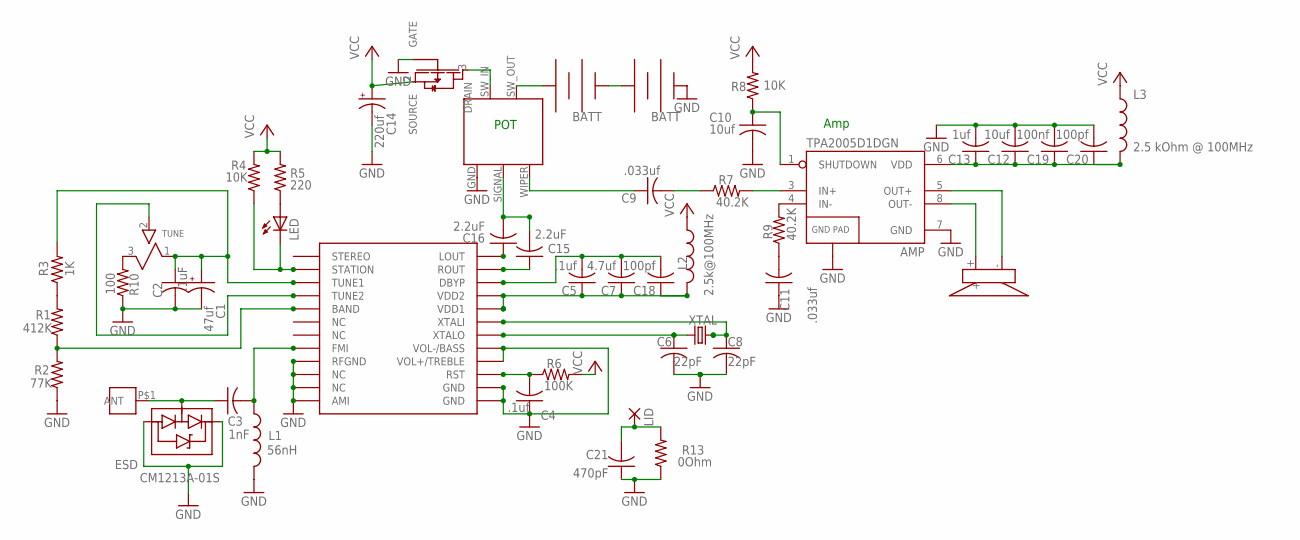
[picture p28: schematic PR5009.sch]

Parts:
AMP: TPA2005D1DGN; POWER-SOP8
ANT: M3_SCREW_POST
C1: 47uf; E2-5
C2: .1uF; C0603
C3: 1nF; C0603
C4, C5: .1uf; C0603
C6, C8: 22pF; C0603
C7: 4.7uf; C0603
C9, C11: .033uf; C0603
C10, C12: 10uf; C0603
C13: 1uf; C0603
C14: 220uf; E2-5
C15, C16: 2.2uF; C0603
C18, C20: 100pf; C0603
C19: 100nf; C0603
C21: 470pF; C0603
ESD: CM1213A-01S; SOT23-3
FET: SI2333DDS
L1: 56nH; 0603
L2: 2.5k@100MHz; 0603
L3: 2.5 kOhm @ 100MHz; 0603
LED: LEDCHIPLED_0805; CHIPLED_0805
LID: 2,54/1,0
R1: 412K; R0603
R2: 77K; R0603
R3: 1K; R0603
R4, R8: 10K; R0603
R5: 220; R0603
R6: 100K; R0603
R7, R9: 40.2K; R0603
R10: 100; R0603
R13: 0Ohm; R0603
TUNE: 10k; 64XR_BOURNS_TRIMPOT
U$1, U$2: BK-92_MPD_AA_BATT_CLIP
U$3: CE32A_DAYTON_SPKR
U$4: SI4831_FM_IC
U$5: RV170SF_TAIWANA_POT_SW
XTAL: CRYSTAL32-SMD; CRYSTAL-32KHZ-SMD

Connections:
GND: AMP.7 (GND), AMP.9 (GND), C1.-, C2.2, C4.1, C6.2, C8.2, C10.2, C11.1, C12.2, C13.2, C14.-, C19.2, C20.2, C21.1, ESD.2 (VP), ESD.3 (VN), FET.1 (GATE), L1.2, R2.1, R10.1, R13.1, U$2.NEG, U$2.NEG@2 (NEG), U$4.AMI, U$4.GND, U$4.GND@2 (GND), U$4.NC@3 (NC), U$4.NC@4 (NC), U$4.RFGND, U$4.VOL+/TREBLE, U$4.VOL-/BASS, U$5.GND
unnamed: AMP.3 (IN+), R7.2
unnamed: AMP.4 (IN-), R9.2
unnamed: C11.2, R9.1
unnamed: C9.2, R7.1
unnamed: C15.2, C16.2, U$5.SIGNAL
unnamed: C5.2, C7.2, C18.2, U$4.DBYP
unnamed: C8.1, U$4.XTALI, XTAL.X1 (1)
unnamed: C4.2, R6.1, U$4.RST
unnamed: LED.C, R4.1, U$4.STATION
unnamed: C6.1, U$4.XTALO, XTAL.X2 (2)
unnamed: LED.A, R5.1
unnamed: TUNE.2, U$4.TUNE2
unnamed: R1.1, R2.2, U$4.BAND
unnamed: U$1.NEG, U$1.NEG@2 (NEG), U$2.POS, U$2.POS@2 (POS)
unnamed: C3.2, L1.1, U$4.FMI
unnamed: C5.1, C7.1, C18.1, L2.2, U$4.VDD1, U$4.VDD2
unnamed: AMP.6 (VDD), C12.1, C13.1, C19.1, C20.1, L3.2
unnamed: AMP.1 (SHUTDOWN), C10.1, R8.1
unnamed: ANT.P$1, C3.1, ESD.1 (CH)
unnamed: R1.2, R3.1
unnamed: U$1.POS, U$1.POS@2 (POS), U$5.SW_OUT
unnamed: C1.+, C2.1, R3.2, TUNE.1, U$4.TUNE1
unnamed: AMP.5 (OUT+), U$3.-
unnamed: AMP.8 (OUT-), U$3.+
unnamed: C9.1, U$5.WIPER
unnamed: R10.2, TUNE.3
unnamed: FET.3 (DRAIN), U$5.SW_IN
unnamed: C15.1, U$4.ROUT
unnamed: C21.2, LID.1, R13.2
unnamed: C16.1, U$4.LOUT
VCC: C14.+, FET.2 (SOURCE), L2.1, L3.1, R4.2, R5.2, R6.2, R8.2

Notes on the sheet:
Amp
POT

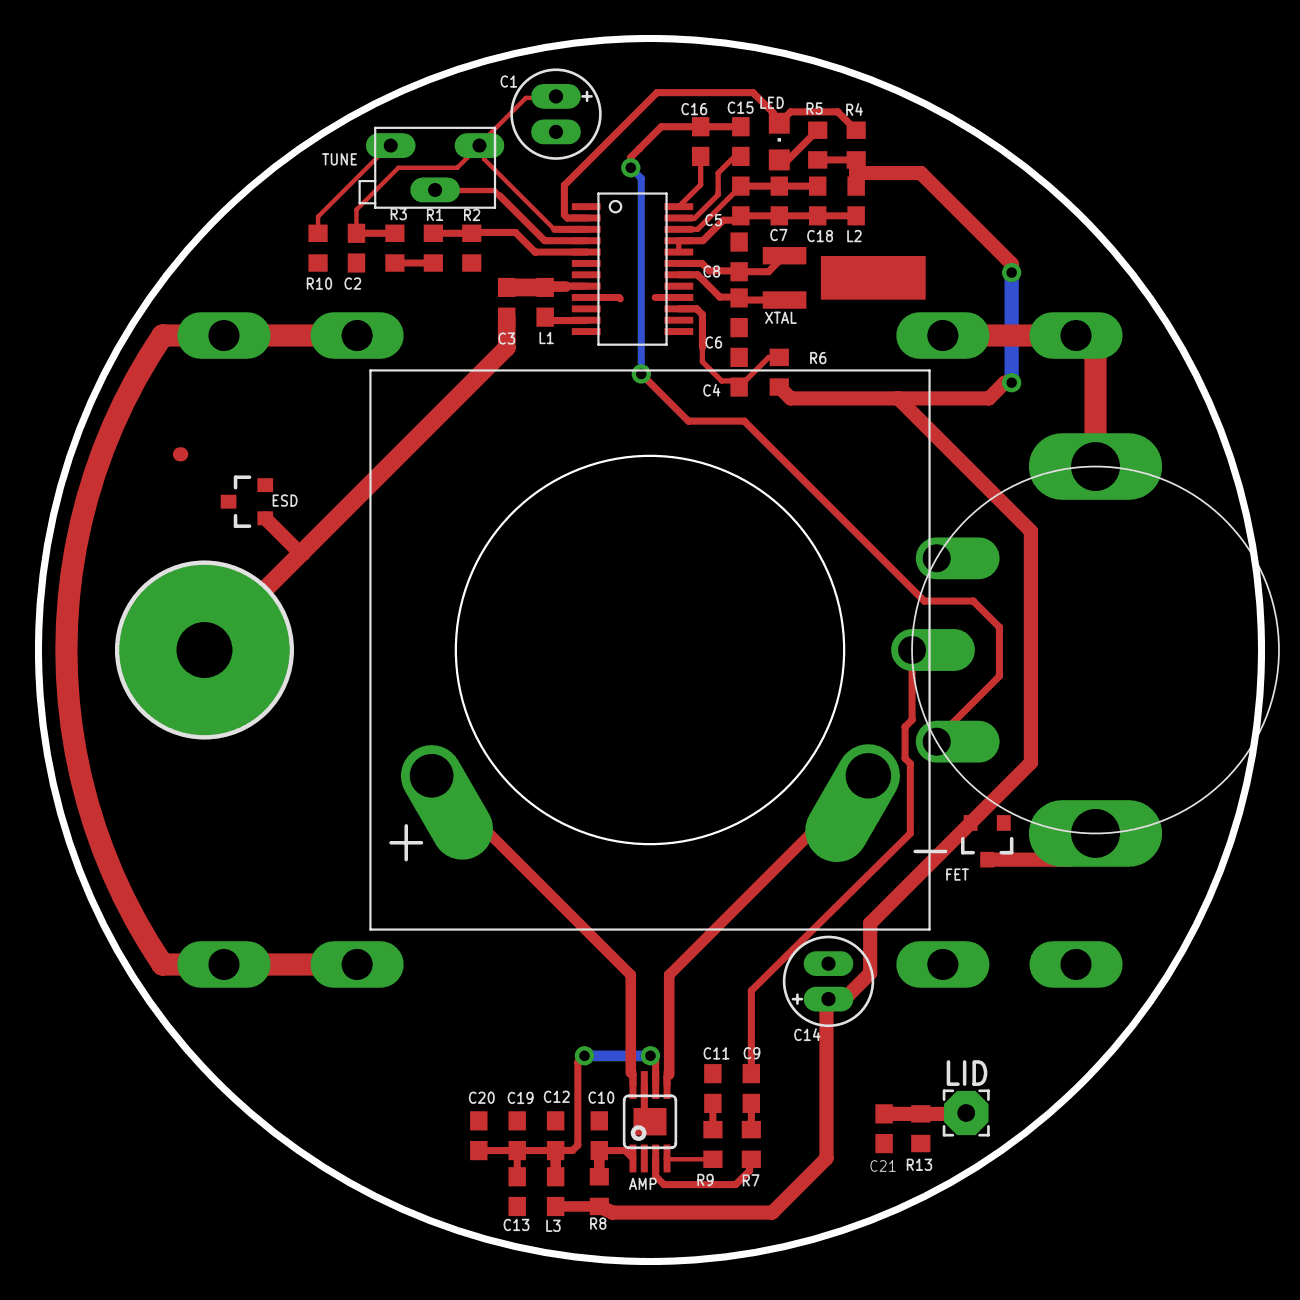
[picture p29: board PR5009.brd from above]

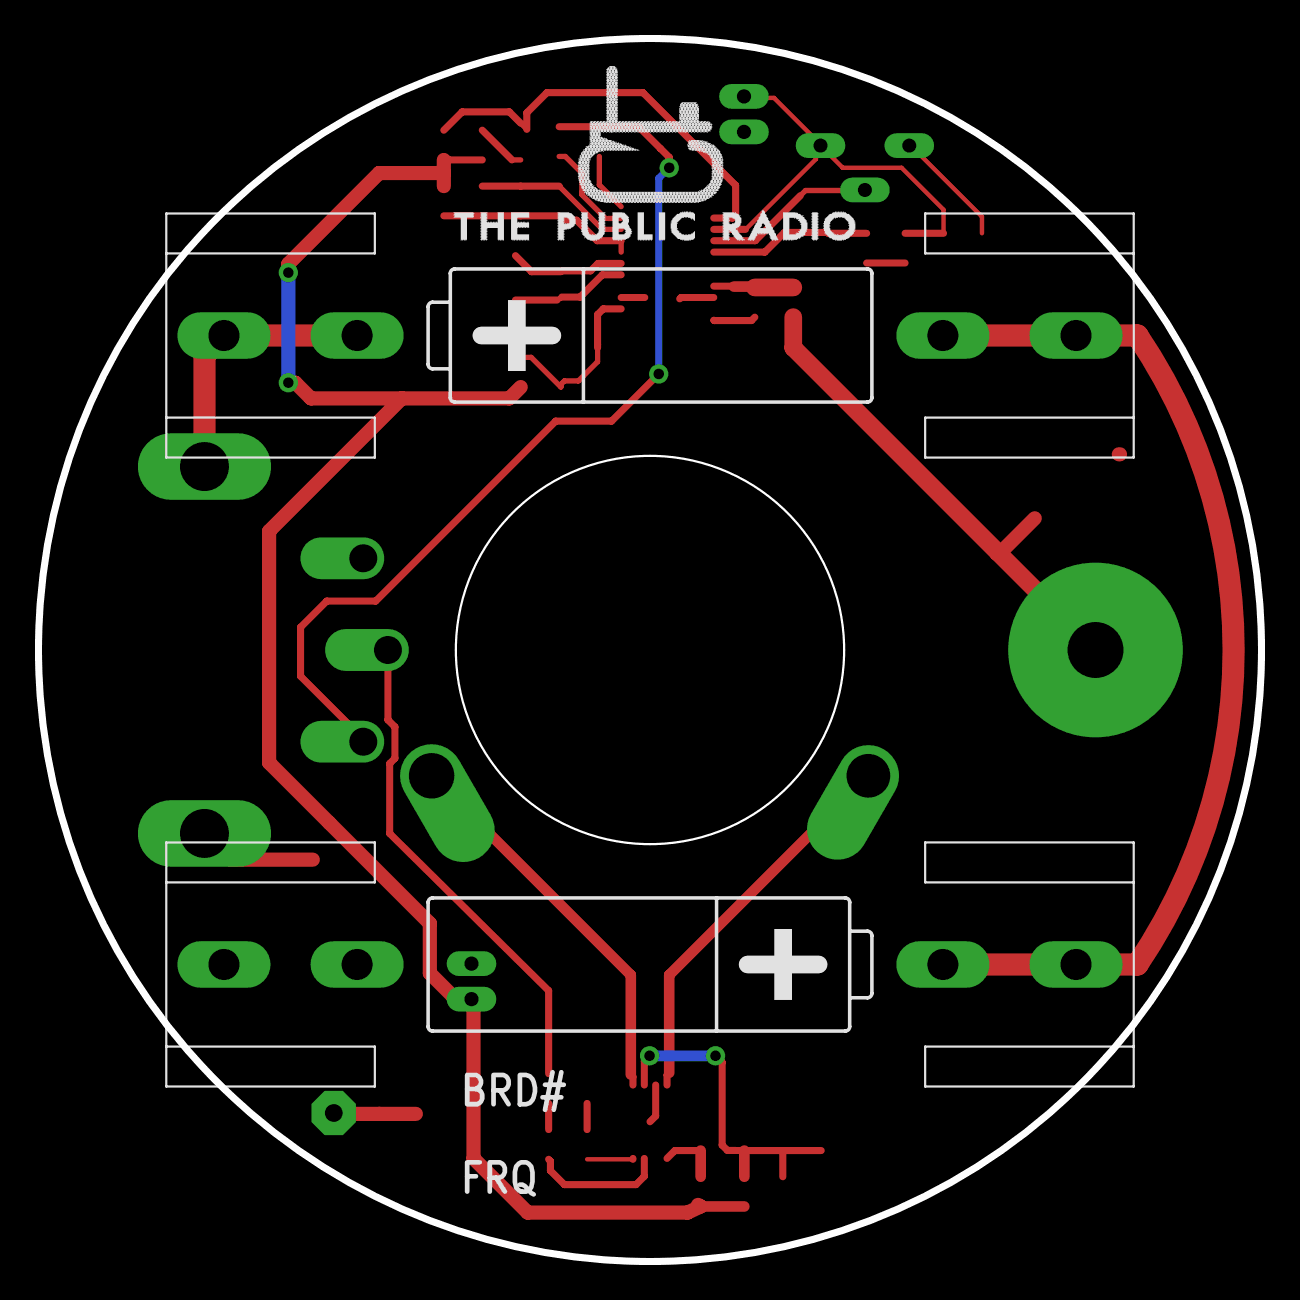
[picture p30: board PR5009.brd from below]

Board: 2 copper layers, 70.0 x 70.0 mm, 47 parts (2 on the bottom side), 32 nets.
