The-Public-Radio/Embedded_Hardware/PR5006.brd

## EAGLE design PR5006.brd (2014-05-17)

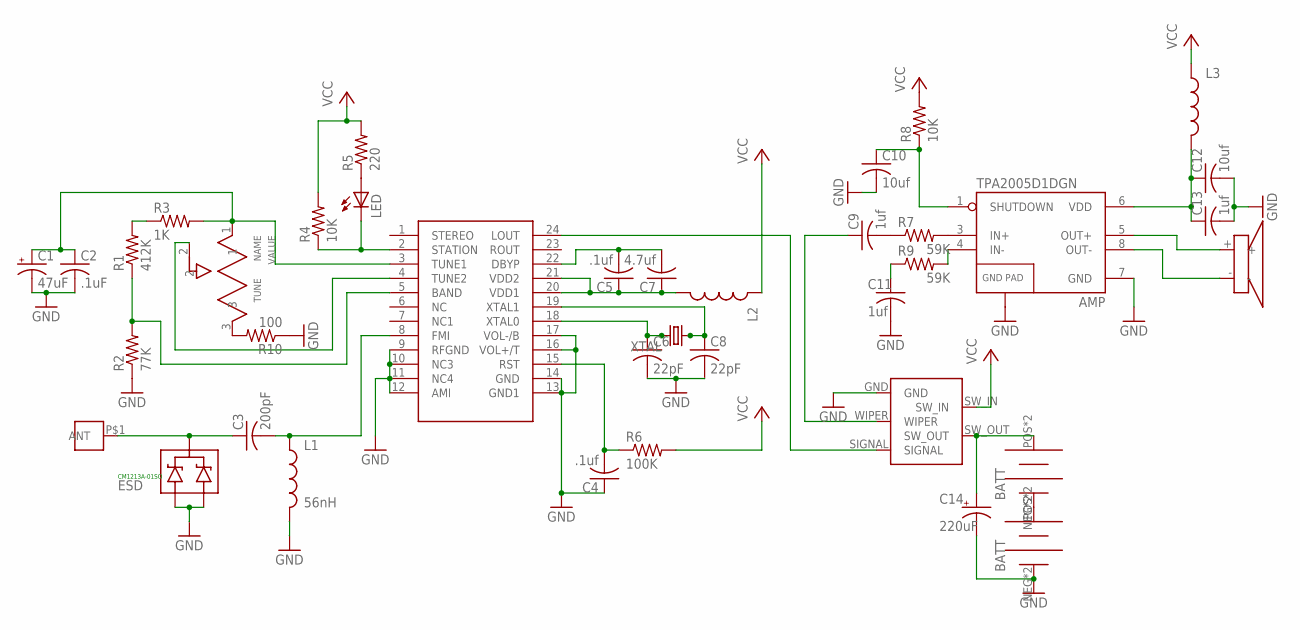
[picture p31: schematic PR5006.sch]

Parts:
AMP: TPA2005D1DGN; POWER-SOP8
ANT: M3_SCREW_POST
C1: 47uF; E2-5
C2: .1uF; C0603
C3: 200pF; C0603
C4, C5: .1uf; C0603
C6, C8: 22pF; C0603
C7: 4.7uf; C0603
C9, C11, C13: 1uf; C0603
C10, C12: 10uf; C0603
C14: 220uF; E2,5-5
ESD: CM1213A-01SO; SOT23-3
L1: 56nH; 0603
L2, L3: INDUCTOR0603; 0603
LED: LEDCHIP-LED0603; CHIP-LED0603
R1: 412K; R0603
R2: 77K; R0603
R3: 1K; R0603
R4, R8: 10K; R0603
R5: 220; R0603
R6: 100K; R0603
R7, R9: 59K; R0603
R10: 100; R0603
SI4831: SI4831-SSOP-24
TUNE: TUNE; 64XR_BOURNS_TRIMPOT
U$1, U$2: BK-92_MPD_AA_BATT_CLIP
U$3: CE32A_DAYTON_SPKR
U$5: P170_BOURNS_POT_SW
XTAL: CRYSTAL32-SMD; CRYSTAL-32KHZ-SMD

Connections:
GND: AMP.7 (GND), AMP.9 (GND), C1.-, C2.2, C4.1, C6.2, C8.2, C10.2, C11.2, C12.2, C13.2, C14.-, ESD.1 (A1), ESD.2 (A2), L1.2, R2.1, R10.1, SI4831.9 (RFGND), SI4831.10 (NC3), SI4831.11 (NC4), SI4831.12 (AMI), SI4831.13 (GND1), SI4831.14 (GND), SI4831.16 (VOL+/T), SI4831.17 (VOL-/B), U$2.NEG, U$2.NEG@2 (NEG), U$5.GND
unnamed: AMP.3 (IN+), R7.2
unnamed: AMP.4 (IN-), R9.2
unnamed: C11.1, R9.1
unnamed: C9.2, R7.1
unnamed: SI4831.24 (LOUT), U$5.SIGNAL
unnamed: C5.2, C7.2, SI4831.22 (DBYP)
unnamed: C8.1, SI4831.19 (XTAL1), XTAL.X1 (1)
unnamed: C4.2, R6.1, SI4831.15 (RST)
unnamed: LED.C, R4.1, SI4831.2 (STATION)
unnamed: C6.1, SI4831.18 (XTAL0), XTAL.X2 (2)
unnamed: LED.A, R5.1
unnamed: SI4831.4 (TUNE2), TUNE.2
unnamed: R1.1, R2.2, SI4831.5 (BAND)
unnamed: U$1.NEG, U$1.NEG@2 (NEG), U$2.POS, U$2.POS@2 (POS)
unnamed: C3.2, L1.1, SI4831.8 (FMI)
unnamed: C5.1, C7.1, L2.2, SI4831.20 (VDD1), SI4831.21 (VDD2)
unnamed: AMP.6 (VDD), C12.1, C13.1, L3.2
unnamed: AMP.1 (SHUTDOWN), C10.1, R8.1
unnamed: ANT.P$1, C3.1, ESD.3 (C)
unnamed: R1.2, R3.1
unnamed: C1.+, C2.1, R3.2, SI4831.3 (TUNE1), TUNE.1
unnamed: AMP.5 (OUT+), U$3.+
unnamed: AMP.8 (OUT-), U$3.-
unnamed: C9.1, U$5.WIPER
unnamed: R10.2, TUNE.3
unnamed: C14.+, U$1.POS, U$1.POS@2 (POS), U$5.SW_OUT
VCC: L2.1, L3.1, R4.2, R5.2, R6.2, R8.2, U$5.SW_IN

Notes on the sheet:
CM1213A-01SO

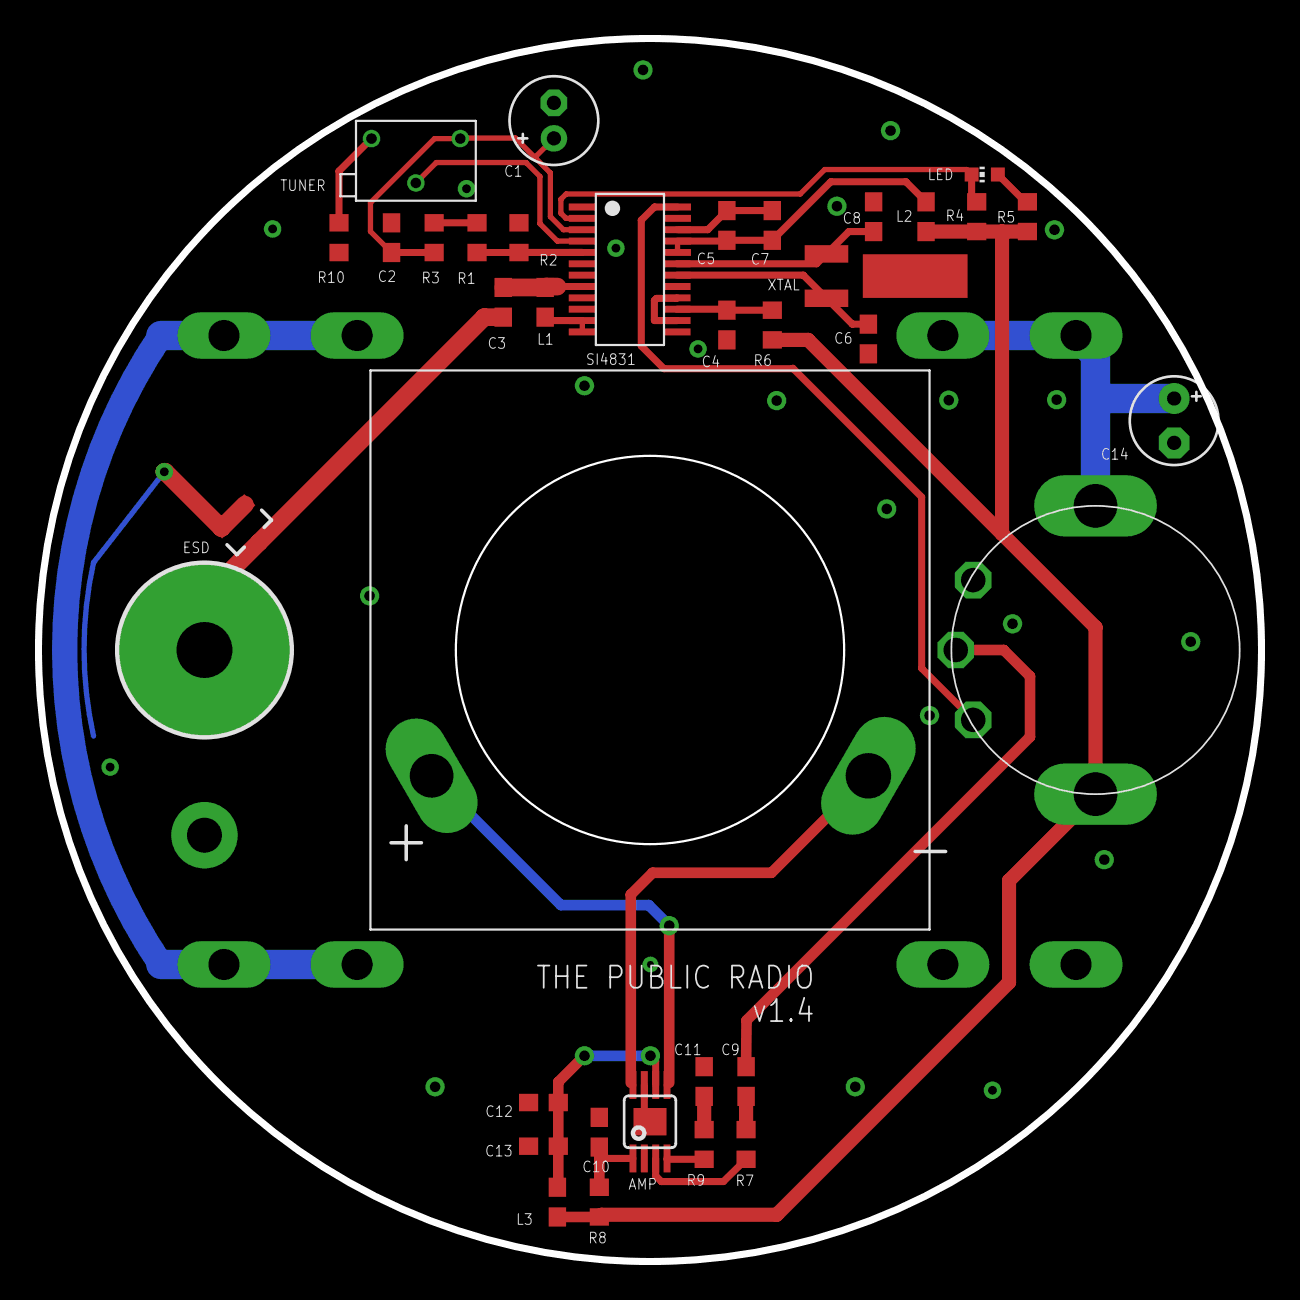
[picture p32: board PR5006.brd from above]

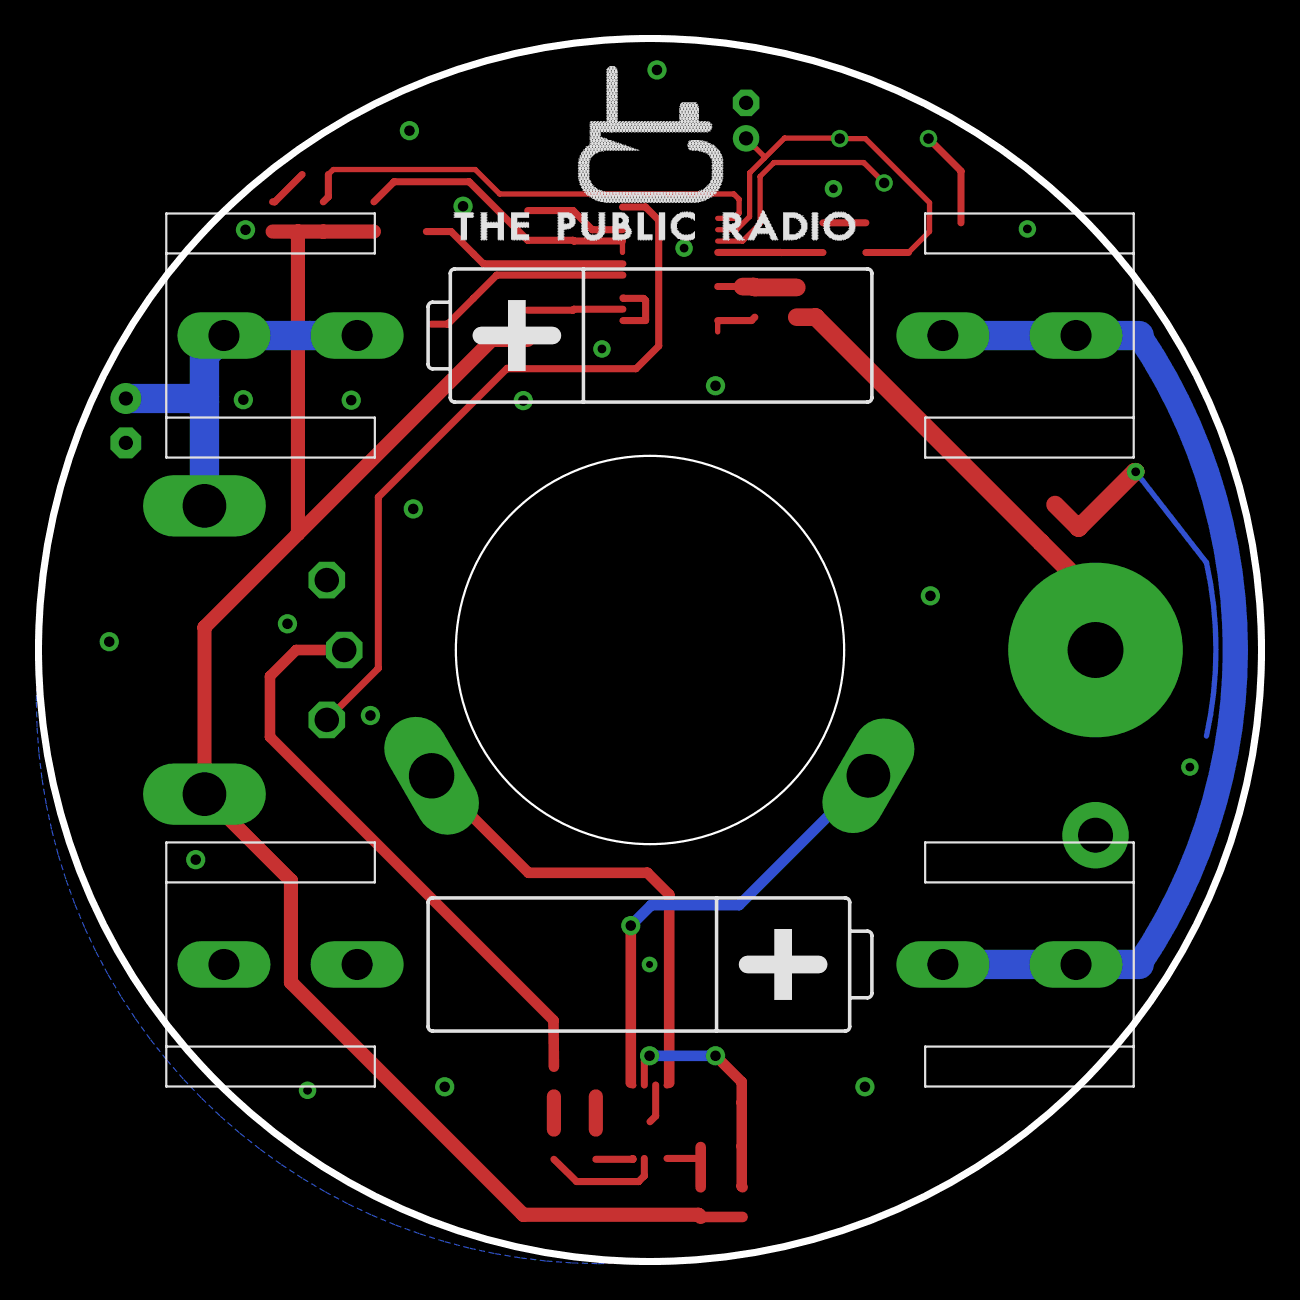
[picture p33: board PR5006.brd from below]

Board: 2 copper layers, 70.0 x 70.0 mm, 38 parts (2 on the bottom side), 28 nets.
