The-Public-Radio/Embedded_Hardware/PR5001 Mini Breakout Shield.brd

## EAGLE design PR5001 Mini Breakout Shield.brd (2014-01-22)

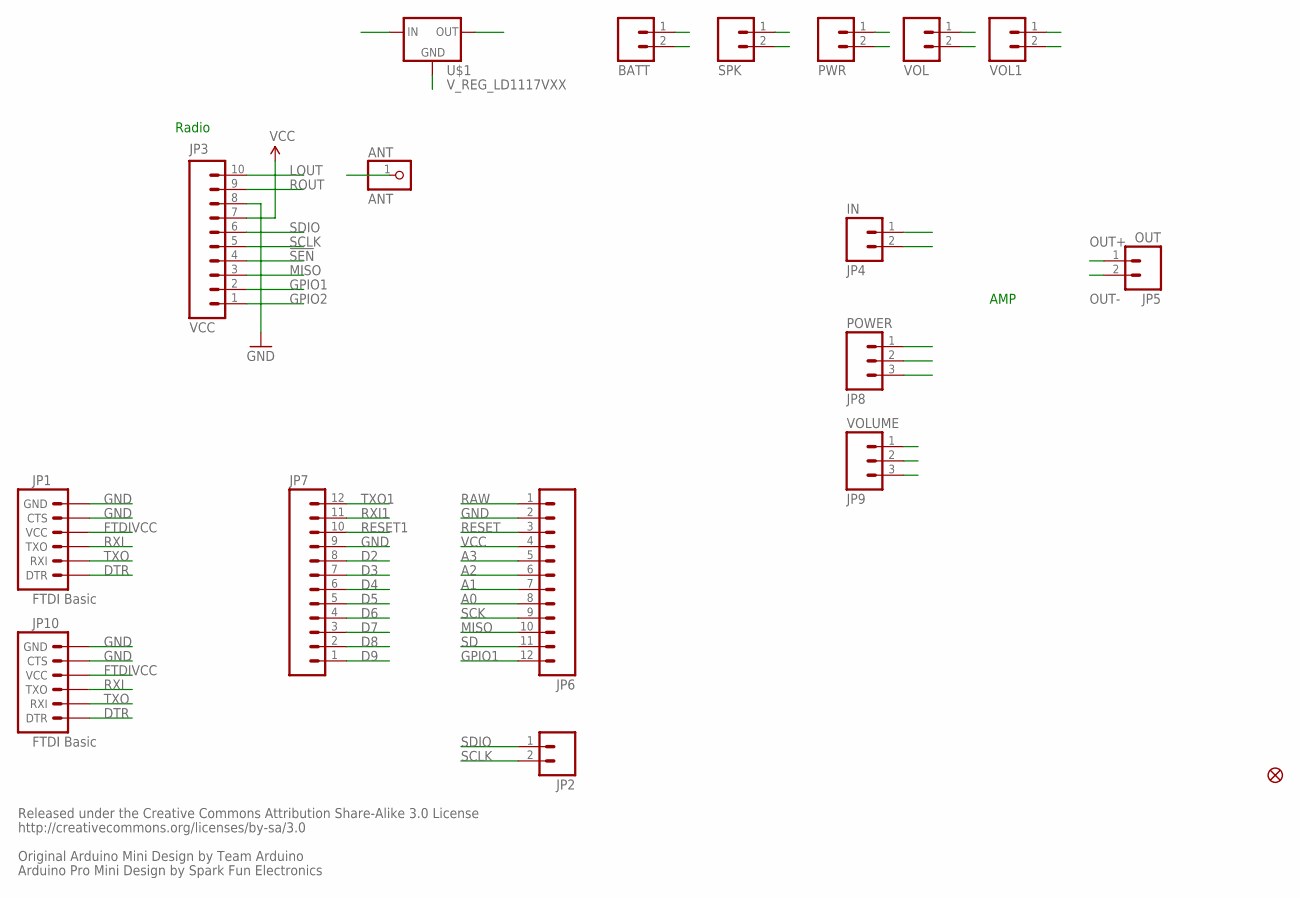
[picture p34: schematic PR5001 Mini Breakout Shield.sch]

Parts:
ANT: ANT; 1X01
BATT: M02PTH; 1X02
JP1, JP10: FTDI Basic; 1X06
JP2: M02PTH; 1X02
JP3: VCC; 1X10
JP4: IN; 1X02
JP5: OUT; 1X02
JP6, JP7: M12PTH; 1X12
JP8: POWER; 1X03
JP9: VOLUME; 1X03
PWR: M02PTH; 1X02
SPK: M02PTH; 1X02
U$1: V_REG_LD1117VXX; 78XXL
U$4: FIDUCIAL1X2; FIDUCIAL-1X2
VOL, VOL1: M02PTH; 1X02

Connections:
!SEN: JP3.4
A0: JP6.8
A1: JP6.7
A2: JP6.6
A3: JP6.5
ANT: ANT.1, VOL1.2
BATT+: BATT.1, PWR.1
D2: JP7.8
D3: JP7.7
D4: JP7.6
D5: JP7.5
D6: JP7.4
D7: JP7.3
D8: JP7.2
D9: JP7.1
DTR: JP1.1 (DTR), JP10.1 (DTR)
FTDIVCC: JP1.4 (VCC), JP10.4 (VCC)
GND: BATT.2, JP1.5 (CTS), JP1.6 (GND), JP3.8, JP4.2, JP6.2, JP7.9, JP8.1, JP9.1, JP10.5 (CTS), JP10.6 (GND), U$1.IN (GND), VOL.1
GPIO1: JP3.2, JP6.12
GPIO2: JP3.1
IN: JP9.3, VOL1.1
LOUT: JP3.10, JP4.1
MISO: JP3.3, JP6.10
OPUT: JP9.2, VOL.2
OUT+: JP5.1, SPK.1
OUT-: JP5.2, SPK.2
POT+: PWR.2, U$1.OUT (IN)
RAW: JP6.1
RESET: JP6.3
RESET1: JP7.10
ROUT: JP3.9
RXI: JP1.3 (TXO), JP10.3 (TXO)
RXI1: JP7.11
SCK: JP6.9
SCLK: JP2.2, JP3.5
SD: JP6.11, JP8.3
SDIO: JP2.1, JP3.6
TXO: JP1.2 (RXI), JP10.2 (RXI)
TXO1: JP7.12
VCC: JP3.7, JP6.4, JP8.2, U$1.GND (OUT)

Notes on the sheet:
Released under the Creative Commons Attribution Share-Alike 3.0 License
http://creativecommons.org/licenses/by-sa/3.0
Original Arduino Mini Design by Team Arduino
Arduino Pro Mini Design by Spark Fun Electronics
AMP
Radio

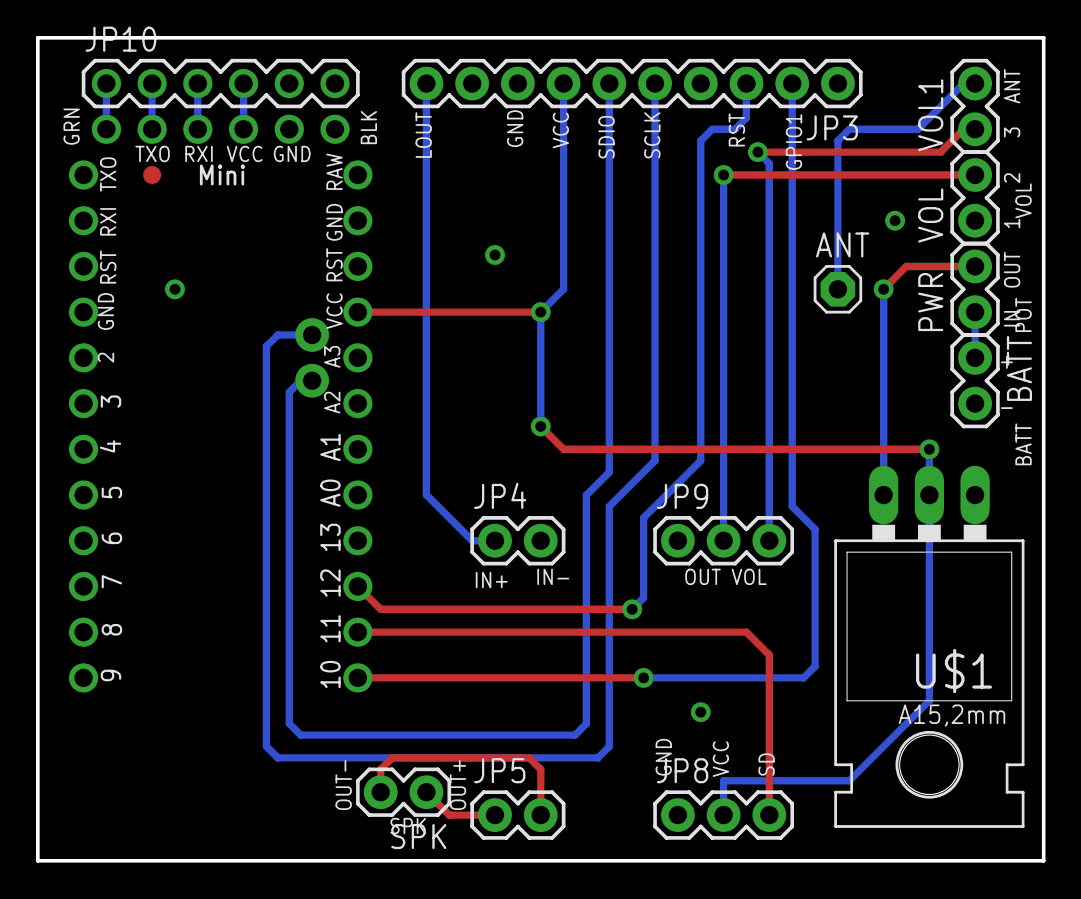
[picture p35: board PR5001 Mini Breakout Shield.brd from above]

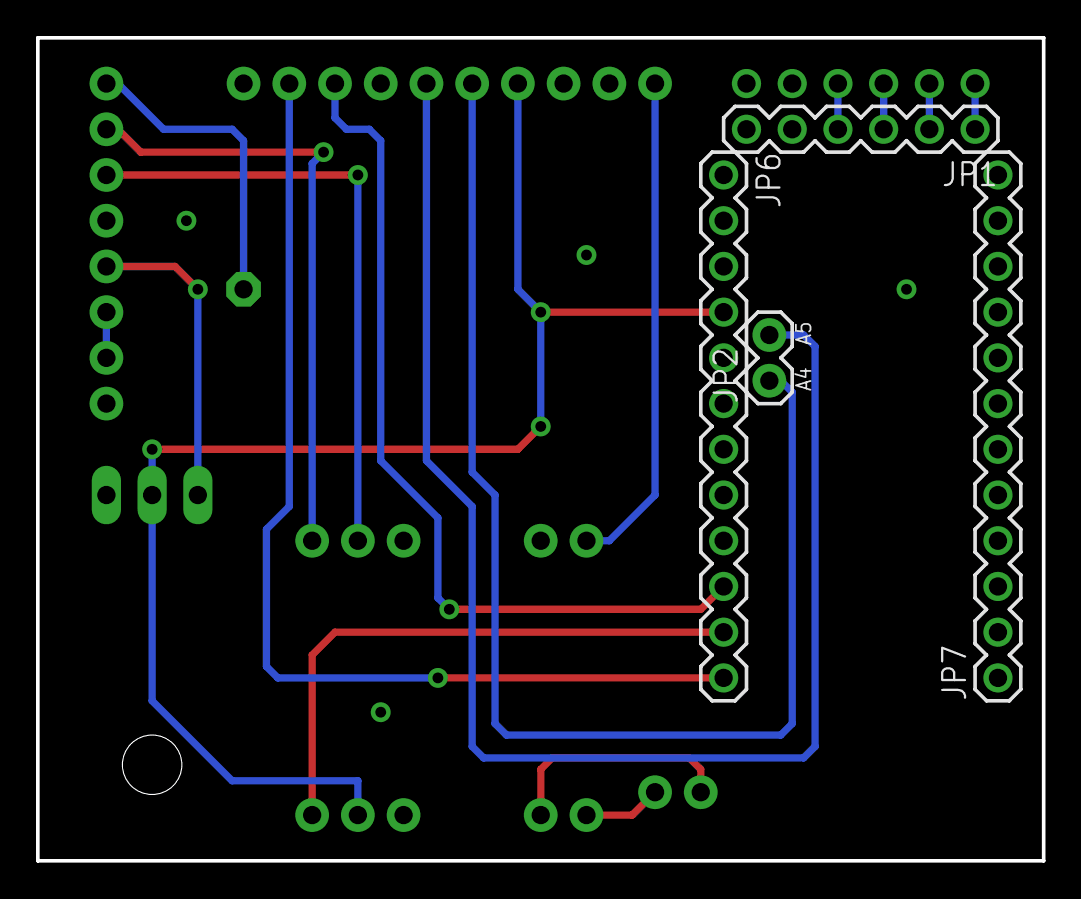
[picture p36: board PR5001 Mini Breakout Shield.brd from below]

Board: 2 copper layers, 55.9 x 45.7 mm, 18 parts (4 on the bottom side), 19 nets.
