The-Public-Radio/Embedded_Hardware/PR5002-S.brd

## EAGLE design PR5002-S.brd (2014-01-22)

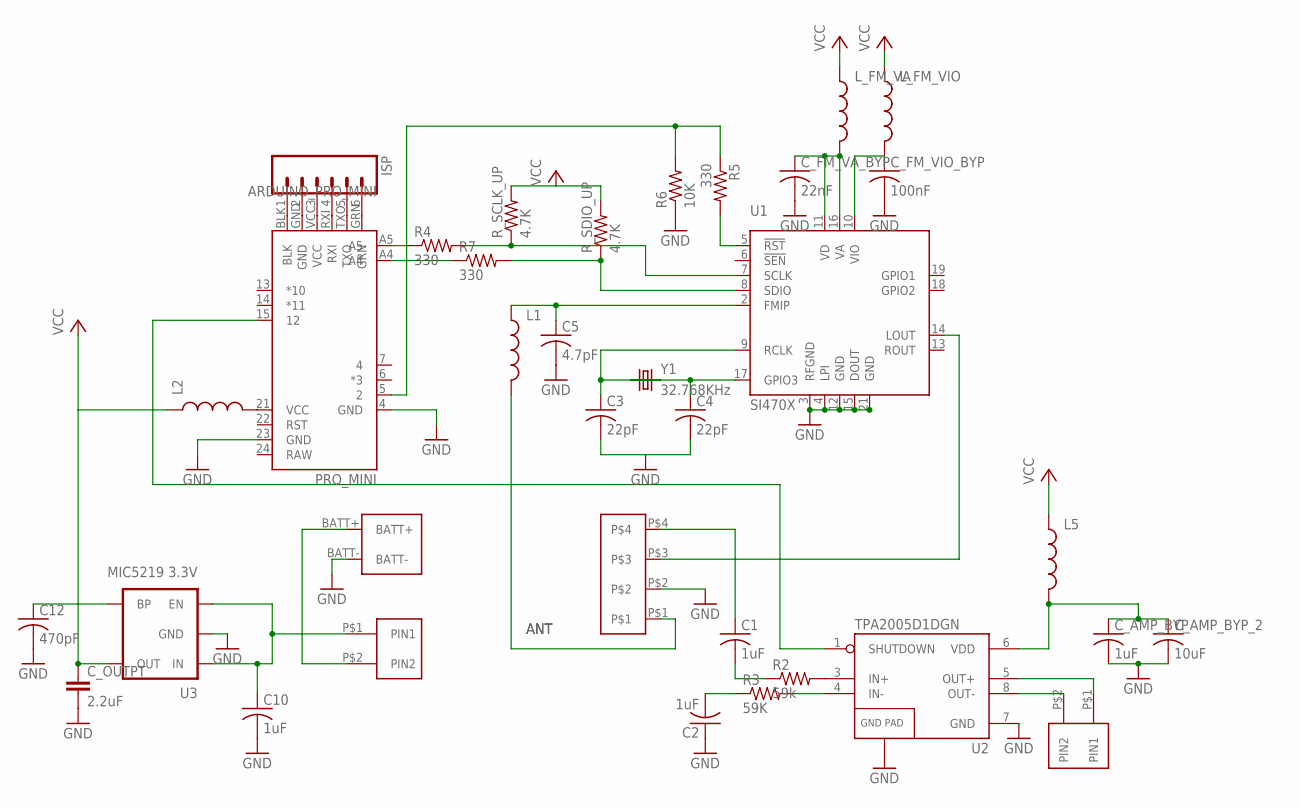
[picture p37: schematic PR5002-S.sch]

Parts:
ANT/POT_VOL: OSTVN04
BATT_IN: KEYSTONE_2479_3XAAA_BOTTOM
C1, C2, C10: 1uF; C0603
C3, C4: 22pF; C0603
C5: 4.7pF; C0603
C12: 470pF; C0603
C_AMP_BYP: 1uF; C0603
C_AMP_BYP_2: 10uF; C0603
C_FM_VA_BYP: 22nF; C0603
C_FM_VIO_BYP: 100nF; C0603
C_OUTPT: 2.2uF; VISHAY_TR3C
ISP: M06LOCK_LONGPADS; 1X06_LOCK_LONGPADS
L1: INDUCTOR0805; 0805
L2, L5: INDUCTOR0603; 0603
L_FM_VA: INDUCTOR0603; 0603
L_FM_VIO: INDUCTOR0603; 0603
POT_SW: OSTVN02
PRO_MINI: ARDUINO_PRO_MINI
R2: 59k; R0603
R3: 59K; R0603
R4, R5, R7: 330; R0603
R6: 10K; R0603
R_SCLK_UP: 4.7K; R0603
R_SDIO_UP: 4.7K; R0603
SPKR: OSTVN02
U1: SI470X
U2: TPA2005D1DGN; POWER-SOP8
U3: MIC5219 3.3V; SOT23-5
Y1: 32.768KHz; CRYSTAL-32KHZ-SMD

Connections:
ANT: ANT/POT_VOL.P$1, L1.2
BATT+: BATT_IN.BATT+, POT_SW.P$2 (PIN2)
GND: ANT/POT_VOL.P$2, BATT_IN.BATT-, C2.1, C3.2, C4.2, C5.2, C10.2, C12.2, C_AMP_BYP.2, C_AMP_BYP_2.2, C_FM_VA_BYP.2, C_FM_VIO_BYP.2, C_OUTPT.P$2 (2), PRO_MINI.4 (GND), PRO_MINI.23 (GND), R6.1, U1.3 (RFGND), U1.4 (LPI), U1.12 (GND), U1.15 (DOUT), U1.21 (GND), U2.7 (GND), U2.9 (GND), U3.2 (GND)
unnamed: C2.2, R3.1
unnamed: C1.2, R2.1
unnamed: C3.1, U1.9 (RCLK), Y1.X2 (2)
unnamed: R5.2, U1.5 (!RST)
unnamed: PRO_MINI.A5, R4.1
unnamed: R4.2, R_SCLK_UP.1, U1.7 (SCLK)
unnamed: PRO_MINI.A4, R7.1
unnamed: PRO_MINI.5 (2), R5.1, R6.2
unnamed: R7.2, R_SDIO_UP.1, U1.8 (SDIO)
unnamed: C5.1, L1.1, U1.2 (FMIP)
unnamed: C4.1, U1.17 (GPIO3), Y1.X1 (1)
unnamed: ISP.6, PRO_MINI.GRN
unnamed: ISP.5, PRO_MINI.TXO
unnamed: R2.2, U2.3 (IN+)
unnamed: R3.2, U2.4 (IN-)
unnamed: SPKR.P$2 (PIN2), U2.8 (OUT-)
unnamed: SPKR.P$1 (PIN1), U2.5 (OUT+)
unnamed: ISP.4, PRO_MINI.RXI
unnamed: ANT/POT_VOL.P$3, U1.14 (LOUT)
unnamed: C10.1, POT_SW.P$1 (PIN1), U3.1 (IN), U3.3 (EN)
unnamed: ISP.3, PRO_MINI.VCC
unnamed: ISP.2, PRO_MINI.GND
unnamed: ISP.1, PRO_MINI.BLK
unnamed: PRO_MINI.15 (12), U2.1 (SHUTDOWN)
unnamed: ANT/POT_VOL.P$4, C1.1
unnamed: C12.1, U3.4 (BP)
unnamed: L2.2, PRO_MINI.21 (VCC)
unnamed: C_FM_VIO_BYP.1, L_FM_VIO.2, U1.10 (VIO)
unnamed: C_FM_VA_BYP.1, L_FM_VA.2, U1.11 (VD), U1.16 (VA)
unnamed: C_AMP_BYP.1, C_AMP_BYP_2.1, L5.2, U2.6 (VDD)
VCC: C_OUTPT.P$1 (1), L2.1, L5.1, L_FM_VA.1, L_FM_VIO.1, R_SCLK_UP.2, R_SDIO_UP.2, U3.5 (OUT)

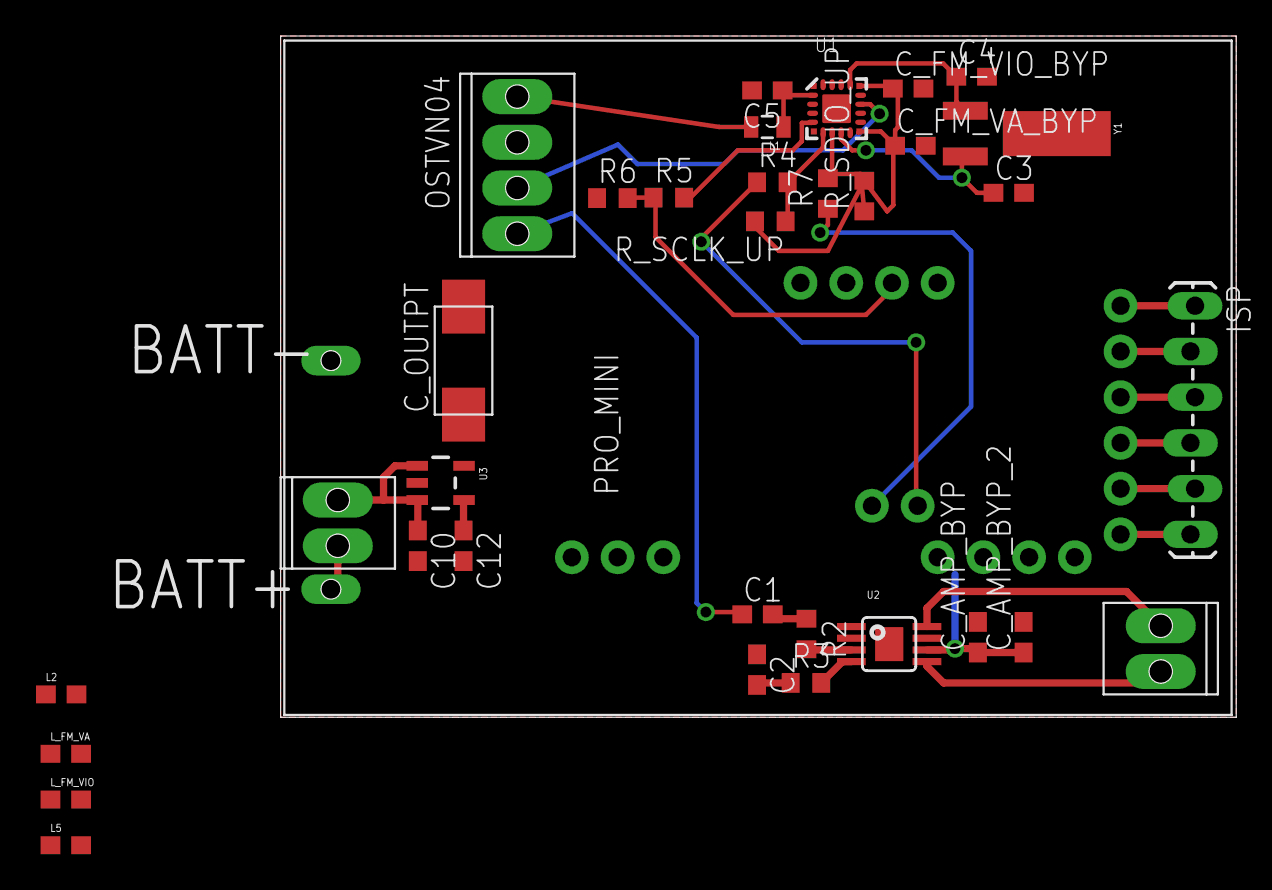
[picture p38: board PR5002-S.brd from above]

Board: 2 copper layers, 53.1 x 37.8 mm, 35 parts (0 on the bottom side), 34 nets.
