The-Public-Radio/Embedded_Hardware/PR5003.brd

## EAGLE design PR5003.brd (2014-01-27)

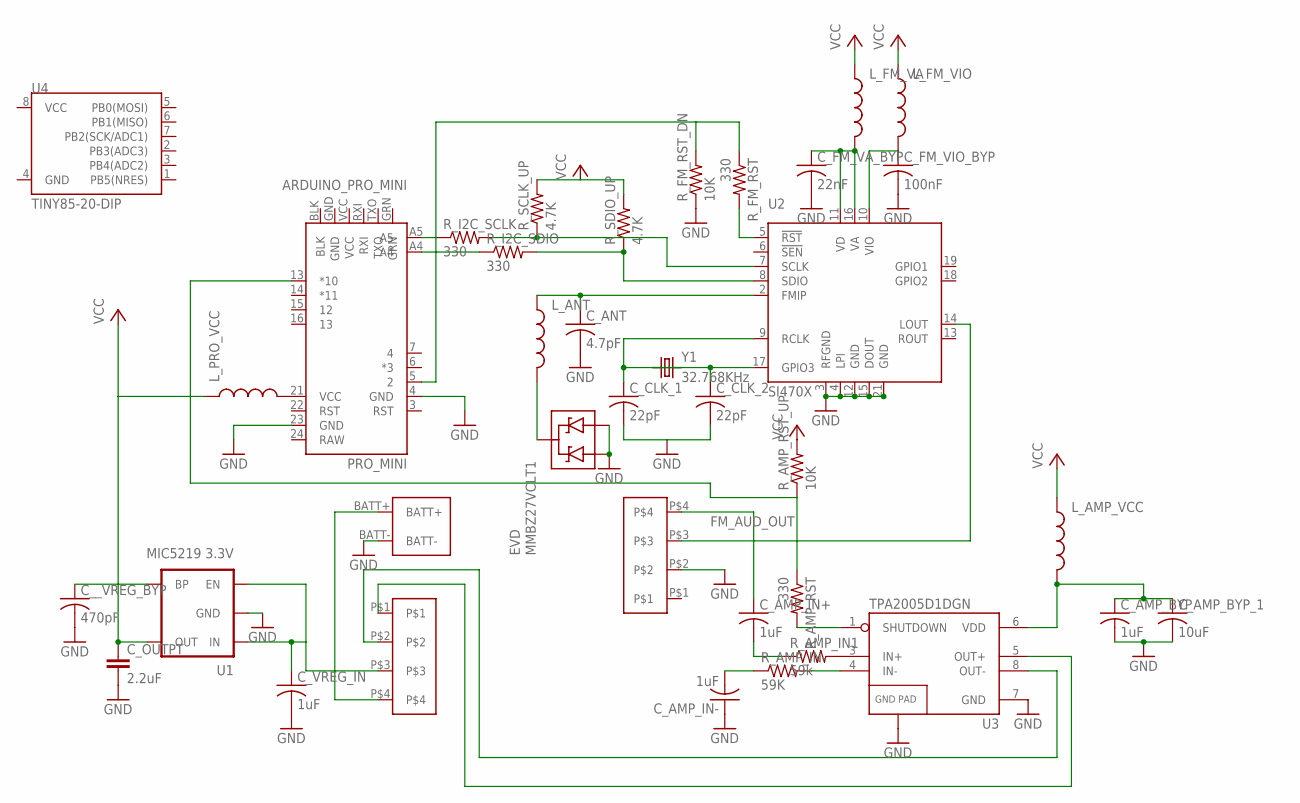
[picture p39: schematic PR5004.sch]

Parts:
ANT/POT_VOL, ANT/POT_VOL1: OSTVN04
BATT_IN: KEYSTONE_2479_3XAAA_BOTTOM
C_AMP_BYP: 1uF; C0603
C_AMP_BYP_1: 10uF; C0603
C_AMP_IN+: 1uF; C0603
C_AMP_IN-: 1uF; C0603
C_ANT: 4.7pF; C0805
C_CLK_1, C_CLK_2: 22pF; C0603
C_FM_VA_BYP: 22nF; C0603
C_FM_VIO_BYP: 100nF; C0603
C_OUTPT: 2.2uF; VISHAY_TR3C
C_VREG_IN: 1uF; C0603
C__VREG_BYP: 470pF; C0603
EVD: MMBZ27VCLT1; SOT23-3
L_AMP_VCC: INDUCTOR0603; 0603
L_ANT: INDUCTOR0805; 0805
L_FM_VA: INDUCTOR0603; 0603
L_FM_VIO: INDUCTOR0603; 0603
L_PRO_VCC: INDUCTOR0603; 0603
PRO_MINI: ARDUINO_PRO_MINI
R_AMP_IN1: 59k; R0603
R_AMP_IN-: 59K; R0603
R_AMP_RST: 330; R0603
R_AMP_RST_UP: 10K; R0603
R_FM_RST: 330; R0603
R_FM_RST_DN: 10K; R0603
R_I2C_SCLK, R_I2C_SDIO: 330; R0603
R_SCLK_UP: 4.7K; R0603
R_SDIO_UP: 4.7K; R0603
U1: MIC5219 3.3V; SOT23-5
U2: SI470X
U3: TPA2005D1DGN; POWER-SOP8
U4: TINY85-20-DIP; DIP08
Y1: 32.768KHz; CRYSTAL-32KHZ-SMD

Connections:
ANT: ANT/POT_VOL.P$1, EVD.3 (C), L_ANT.2
BATT+: ANT/POT_VOL1.P$4, BATT_IN.BATT+
FM_AUD_OUT: ANT/POT_VOL.P$3, U2.14 (LOUT)
GND: ANT/POT_VOL.P$2, BATT_IN.BATT-, C_AMP_BYP.2, C_AMP_BYP_1.2, C_AMP_IN-.1, C_ANT.2, C_CLK_1.2, C_CLK_2.2, C_FM_VA_BYP.2, C_FM_VIO_BYP.2, C_OUTPT.P$2 (2), C_VREG_IN.2, C__VREG_BYP.2, EVD.1 (A1), EVD.2 (A2), PRO_MINI.4 (GND), PRO_MINI.23 (GND), PRO_MINI.BLK, PRO_MINI.GND, R_FM_RST_DN.1, U1.2 (GND), U2.3 (RFGND), U2.4 (LPI), U2.12 (GND), U2.15 (DOUT), U2.21 (GND), U3.7 (GND), U3.9 (GND); also elsewhere on the board
unnamed: C_AMP_IN-.2, R_AMP_IN-.1
unnamed: C_AMP_IN+.2, R_AMP_IN1.1
unnamed: C_CLK_1.1, U2.9 (RCLK), Y1.X2 (2)
unnamed: R_FM_RST.2, U2.5 (!RST)
unnamed: PRO_MINI.A5, R_I2C_SCLK.1
unnamed: R_I2C_SCLK.2, R_SCLK_UP.1, U2.7 (SCLK)
unnamed: PRO_MINI.A4, R_I2C_SDIO.1
unnamed 11: PRO_MINI.15 (12); also elsewhere on the board
unnamed: R_I2C_SDIO.2, R_SDIO_UP.1, U2.8 (SDIO)
unnamed: C_ANT.1, L_ANT.1, U2.2 (FMIP)
unnamed: C_CLK_2.1, U2.17 (GPIO3), Y1.X1 (1)
unnamed 15: PRO_MINI.GRN; also elsewhere on the board
unnamed 16: PRO_MINI.TXO; also elsewhere on the board
unnamed: R_AMP_IN1.2, U3.3 (IN+)
unnamed: R_AMP_IN-.2, U3.4 (IN-)
unnamed: ANT/POT_VOL1.P$2, U3.8 (OUT-)
unnamed: ANT/POT_VOL1.P$1, U3.5 (OUT+)
unnamed 21: PRO_MINI.RXI; also elsewhere on the board
unnamed: R_AMP_RST.2, U3.1 (SHUTDOWN)
unnamed: ANT/POT_VOL1.P$3, C_VREG_IN.1, U1.1 (IN), U1.3 (EN)
unnamed 24: PRO_MINI.VCC; also elsewhere on the board
unnamed 25: PRO_MINI.3 (RST); also elsewhere on the board
unnamed: PRO_MINI.5 (2), R_FM_RST.1, R_FM_RST_DN.2
unnamed 27: PRO_MINI.14 (*11); also elsewhere on the board
unnamed: PRO_MINI.13 (*10), R_AMP_RST.1, R_AMP_RST_UP.1
unnamed 29: PRO_MINI.16 (13); also elsewhere on the board
unnamed: ANT/POT_VOL.P$4, C_AMP_IN+.1
unnamed: C__VREG_BYP.1, U1.4 (BP)
unnamed: L_PRO_VCC.2, PRO_MINI.21 (VCC)
unnamed: C_FM_VIO_BYP.1, L_FM_VIO.2, U2.10 (VIO)
unnamed: C_FM_VA_BYP.1, L_FM_VA.2, U2.11 (VD), U2.16 (VA)
unnamed: C_AMP_BYP.1, C_AMP_BYP_1.1, L_AMP_VCC.2, U3.6 (VDD)
VCC: C_OUTPT.P$1 (1), L_AMP_VCC.1, L_FM_VA.1, L_FM_VIO.1, L_PRO_VCC.1, R_AMP_RST_UP.2, R_SCLK_UP.2, R_SDIO_UP.2, U1.5 (OUT); also elsewhere on the board

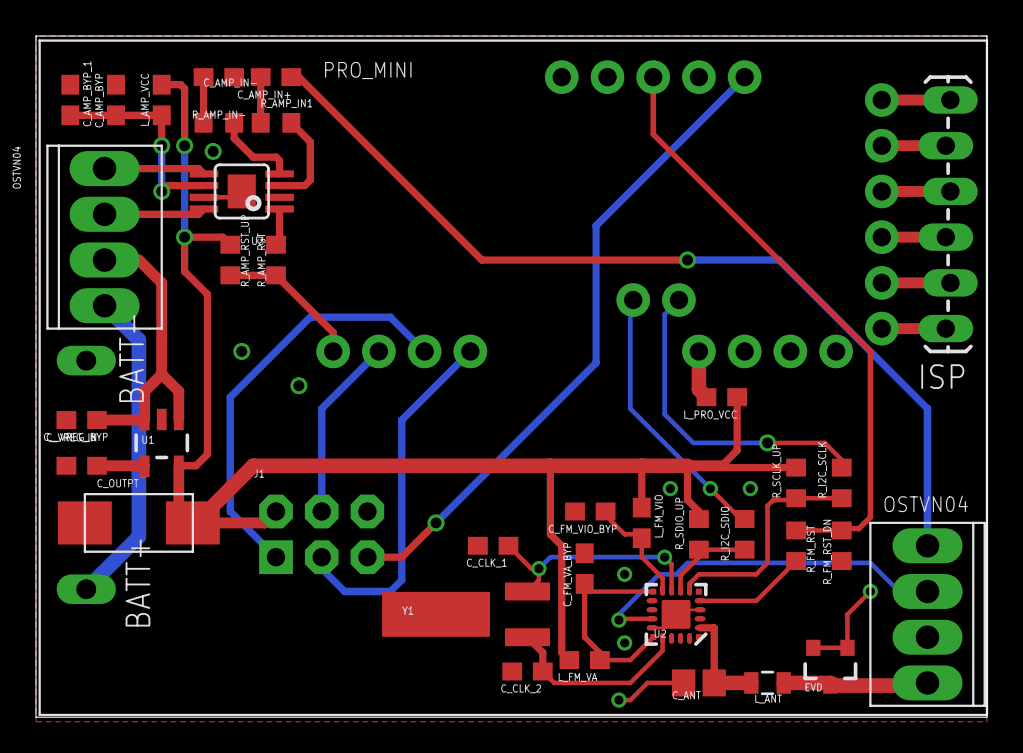
[picture p40: board PR5003.brd from above]

Board: 2 copper layers, 52.8 x 37.8 mm, 38 parts (0 on the bottom side), 37 nets.

Other parts of the board:
ISP: 1X06_LOCK_LONGPADS
J1: AVR_SPI_PRG_6NS; 2X3-NS

Their connections:
GND: ISP.1, ISP.2, J1.6; also elsewhere on the board
unnamed 11: J1.1; also elsewhere on the board
unnamed 15: ISP.6; also elsewhere on the board
unnamed 16: ISP.5; also elsewhere on the board
unnamed 21: ISP.4; also elsewhere on the board
unnamed 24: ISP.3; also elsewhere on the board
unnamed 25: J1.5; also elsewhere on the board
unnamed 27: J1.4; also elsewhere on the board
unnamed 29: J1.3; also elsewhere on the board
VCC: J1.2; also elsewhere on the board
